elektrojupp/public_transport_map_berlin/hw/20xLED_001.kicad_sch

## KiCad design hw/20xLED_001.kicad_sch (2026-01-20)

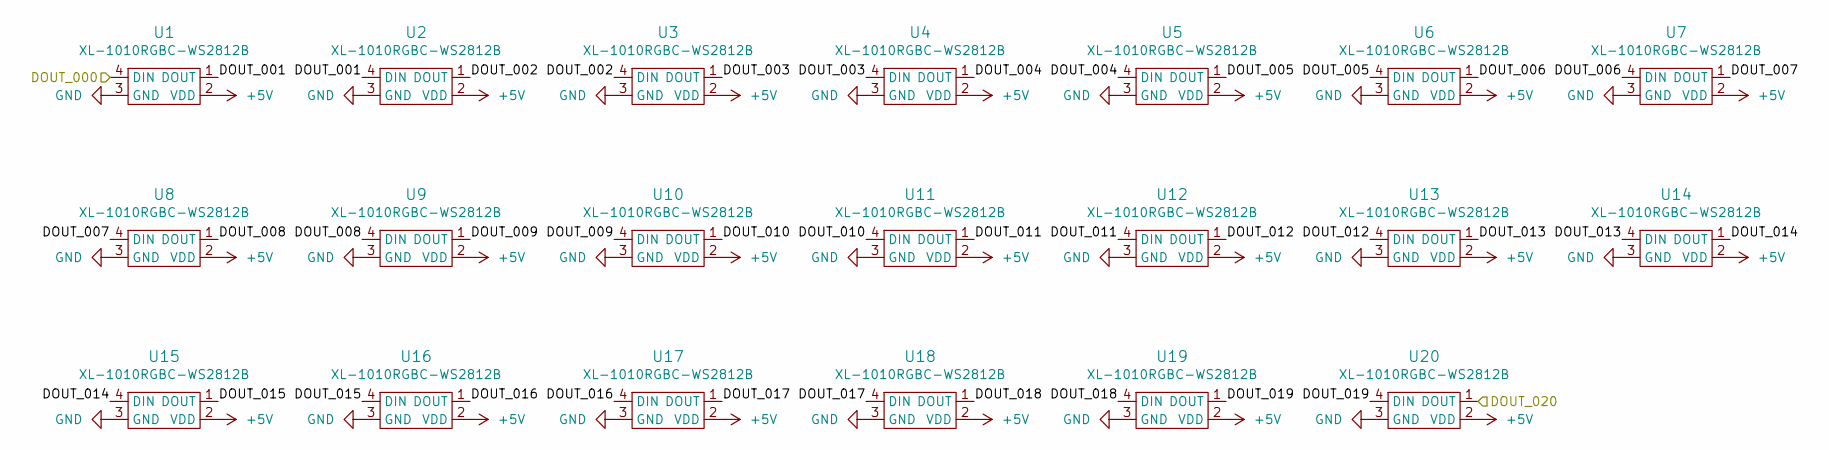
[picture p3: schematic 20xLED_001.kicad_sch]

Parts:
U1, U2, U3, U4, U5, U6, U7, U8, U9, U10, U11, U12, U13, U14, U15, U16, U17, U18, U19, U20: XL-1010RGBC-WS2812B; SMD-4P,1.1x1.1mm; LCSC C5349953

Connections:
+5V: U1.2 (VDD), U2.2 (VDD), U3.2 (VDD), U4.2 (VDD), U5.2 (VDD), U6.2 (VDD), U7.2 (VDD), U8.2 (VDD), U9.2 (VDD), U10.2 (VDD), U11.2 (VDD), U12.2 (VDD), U13.2 (VDD), U14.2 (VDD), U15.2 (VDD), U16.2 (VDD), U17.2 (VDD), U18.2 (VDD), U19.2 (VDD), U20.2 (VDD)
DOUT_000: U1.4 (DIN)
DOUT_001: U1.1 (DOUT), U2.4 (DIN)
DOUT_002: U2.1 (DOUT), U3.4 (DIN)
DOUT_003: U3.1 (DOUT), U4.4 (DIN)
DOUT_004: U4.1 (DOUT), U5.4 (DIN)
DOUT_005: U5.1 (DOUT), U6.4 (DIN)
DOUT_006: U6.1 (DOUT), U7.4 (DIN)
DOUT_007: U7.1 (DOUT), U8.4 (DIN)
DOUT_008: U8.1 (DOUT), U9.4 (DIN)
DOUT_009: U9.1 (DOUT), U10.4 (DIN)
DOUT_010: U10.1 (DOUT), U11.4 (DIN)
DOUT_011: U11.1 (DOUT), U12.4 (DIN)
DOUT_012: U12.1 (DOUT), U13.4 (DIN)
DOUT_013: U13.1 (DOUT), U14.4 (DIN)
DOUT_014: U14.1 (DOUT), U15.4 (DIN)
DOUT_015: U15.1 (DOUT), U16.4 (DIN)
DOUT_016: U16.1 (DOUT), U17.4 (DIN)
DOUT_017: U17.1 (DOUT), U18.4 (DIN)
DOUT_018: U18.1 (DOUT), U19.4 (DIN)
DOUT_019: U19.1 (DOUT), U20.4 (DIN)
DOUT_020: U20.1 (DOUT)
GND: U1.3 (GND), U2.3 (GND), U3.3 (GND), U4.3 (GND), U5.3 (GND), U6.3 (GND), U7.3 (GND), U8.3 (GND), U9.3 (GND), U10.3 (GND), U11.3 (GND), U12.3 (GND), U13.3 (GND), U14.3 (GND), U15.3 (GND), U16.3 (GND), U17.3 (GND), U18.3 (GND), U19.3 (GND), U20.3 (GND)
