elektrojupp/public_transport_map_berlin/hw/20xLED_002.kicad_sch

## KiCad design hw/20xLED_002.kicad_sch (2026-01-20)

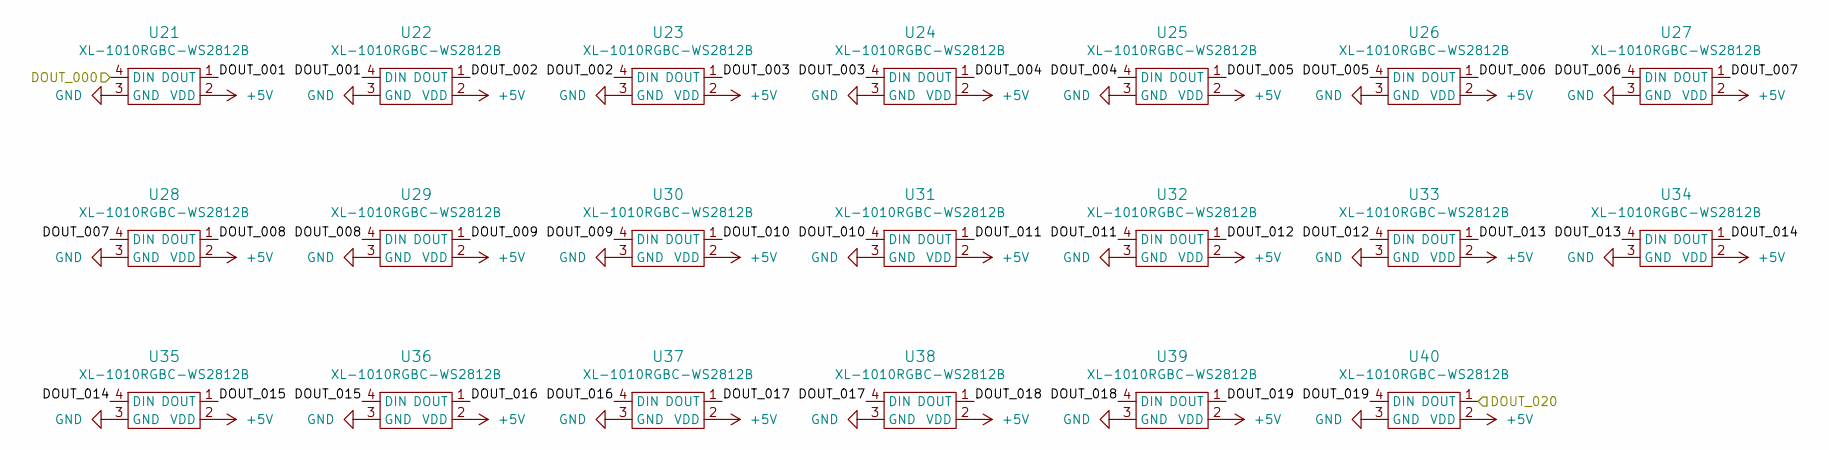
[picture p4: schematic 20xLED_002.kicad_sch]

Parts:
U21, U22, U23, U24, U25, U26, U27, U28, U29, U30, U31, U32, U33, U34, U35, U36, U37, U38, U39, U40: XL-1010RGBC-WS2812B; SMD-4P,1.1x1.1mm; LCSC C5349953

Connections:
+5V: U21.2 (VDD), U22.2 (VDD), U23.2 (VDD), U24.2 (VDD), U25.2 (VDD), U26.2 (VDD), U27.2 (VDD), U28.2 (VDD), U29.2 (VDD), U30.2 (VDD), U31.2 (VDD), U32.2 (VDD), U33.2 (VDD), U34.2 (VDD), U35.2 (VDD), U36.2 (VDD), U37.2 (VDD), U38.2 (VDD), U39.2 (VDD), U40.2 (VDD)
DOUT_000: U21.4 (DIN)
DOUT_001: U21.1 (DOUT), U22.4 (DIN)
DOUT_002: U22.1 (DOUT), U23.4 (DIN)
DOUT_003: U23.1 (DOUT), U24.4 (DIN)
DOUT_004: U24.1 (DOUT), U25.4 (DIN)
DOUT_005: U25.1 (DOUT), U26.4 (DIN)
DOUT_006: U26.1 (DOUT), U27.4 (DIN)
DOUT_007: U27.1 (DOUT), U28.4 (DIN)
DOUT_008: U28.1 (DOUT), U29.4 (DIN)
DOUT_009: U29.1 (DOUT), U30.4 (DIN)
DOUT_010: U30.1 (DOUT), U31.4 (DIN)
DOUT_011: U31.1 (DOUT), U32.4 (DIN)
DOUT_012: U32.1 (DOUT), U33.4 (DIN)
DOUT_013: U33.1 (DOUT), U34.4 (DIN)
DOUT_014: U34.1 (DOUT), U35.4 (DIN)
DOUT_015: U35.1 (DOUT), U36.4 (DIN)
DOUT_016: U36.1 (DOUT), U37.4 (DIN)
DOUT_017: U37.1 (DOUT), U38.4 (DIN)
DOUT_018: U38.1 (DOUT), U39.4 (DIN)
DOUT_019: U39.1 (DOUT), U40.4 (DIN)
DOUT_020: U40.1 (DOUT)
GND: U21.3 (GND), U22.3 (GND), U23.3 (GND), U24.3 (GND), U25.3 (GND), U26.3 (GND), U27.3 (GND), U28.3 (GND), U29.3 (GND), U30.3 (GND), U31.3 (GND), U32.3 (GND), U33.3 (GND), U34.3 (GND), U35.3 (GND), U36.3 (GND), U37.3 (GND), U38.3 (GND), U39.3 (GND), U40.3 (GND)
