elektrojupp/public_transport_map_berlin/hw/20xLED_003.kicad_sch

## KiCad design hw/20xLED_003.kicad_sch (2026-01-20)

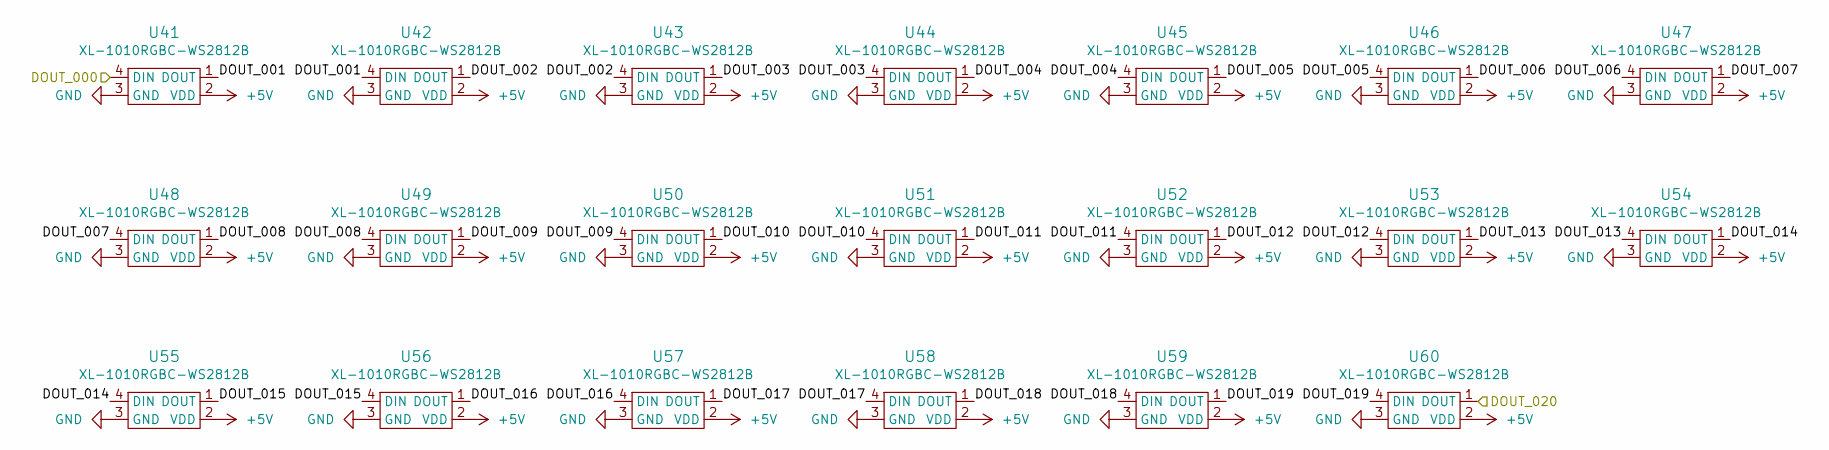
[picture p5: schematic 20xLED_003.kicad_sch]

Parts:
U41, U42, U43, U44, U45, U46, U47, U48, U49, U50, U51, U52, U53, U54, U55, U56, U57, U58, U59, U60: XL-1010RGBC-WS2812B; SMD-4P,1.1x1.1mm; LCSC C5349953

Connections:
+5V: U41.2 (VDD), U42.2 (VDD), U43.2 (VDD), U44.2 (VDD), U45.2 (VDD), U46.2 (VDD), U47.2 (VDD), U48.2 (VDD), U49.2 (VDD), U50.2 (VDD), U51.2 (VDD), U52.2 (VDD), U53.2 (VDD), U54.2 (VDD), U55.2 (VDD), U56.2 (VDD), U57.2 (VDD), U58.2 (VDD), U59.2 (VDD), U60.2 (VDD)
DOUT_000: U41.4 (DIN)
DOUT_001: U41.1 (DOUT), U42.4 (DIN)
DOUT_002: U42.1 (DOUT), U43.4 (DIN)
DOUT_003: U43.1 (DOUT), U44.4 (DIN)
DOUT_004: U44.1 (DOUT), U45.4 (DIN)
DOUT_005: U45.1 (DOUT), U46.4 (DIN)
DOUT_006: U46.1 (DOUT), U47.4 (DIN)
DOUT_007: U47.1 (DOUT), U48.4 (DIN)
DOUT_008: U48.1 (DOUT), U49.4 (DIN)
DOUT_009: U49.1 (DOUT), U50.4 (DIN)
DOUT_010: U50.1 (DOUT), U51.4 (DIN)
DOUT_011: U51.1 (DOUT), U52.4 (DIN)
DOUT_012: U52.1 (DOUT), U53.4 (DIN)
DOUT_013: U53.1 (DOUT), U54.4 (DIN)
DOUT_014: U54.1 (DOUT), U55.4 (DIN)
DOUT_015: U55.1 (DOUT), U56.4 (DIN)
DOUT_016: U56.1 (DOUT), U57.4 (DIN)
DOUT_017: U57.1 (DOUT), U58.4 (DIN)
DOUT_018: U58.1 (DOUT), U59.4 (DIN)
DOUT_019: U59.1 (DOUT), U60.4 (DIN)
DOUT_020: U60.1 (DOUT)
GND: U41.3 (GND), U42.3 (GND), U43.3 (GND), U44.3 (GND), U45.3 (GND), U46.3 (GND), U47.3 (GND), U48.3 (GND), U49.3 (GND), U50.3 (GND), U51.3 (GND), U52.3 (GND), U53.3 (GND), U54.3 (GND), U55.3 (GND), U56.3 (GND), U57.3 (GND), U58.3 (GND), U59.3 (GND), U60.3 (GND)
