elektrojupp/public_transport_map_berlin/hw/20xLED_004.kicad_sch

## KiCad design hw/20xLED_004.kicad_sch (2026-01-20)

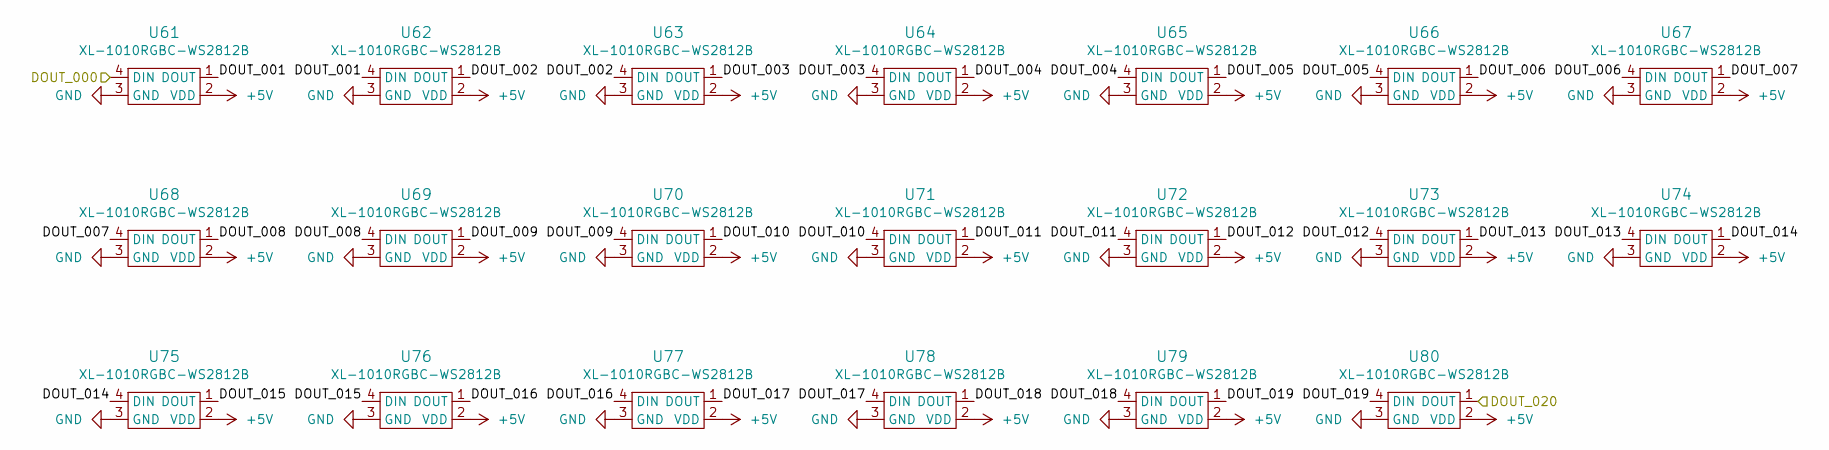
[picture p6: schematic 20xLED_004.kicad_sch]

Parts:
U61, U62, U63, U64, U65, U66, U67, U68, U69, U70, U71, U72, U73, U74, U75, U76, U77, U78, U79, U80: XL-1010RGBC-WS2812B; SMD-4P,1.1x1.1mm; LCSC C5349953

Connections:
+5V: U61.2 (VDD), U62.2 (VDD), U63.2 (VDD), U64.2 (VDD), U65.2 (VDD), U66.2 (VDD), U67.2 (VDD), U68.2 (VDD), U69.2 (VDD), U70.2 (VDD), U71.2 (VDD), U72.2 (VDD), U73.2 (VDD), U74.2 (VDD), U75.2 (VDD), U76.2 (VDD), U77.2 (VDD), U78.2 (VDD), U79.2 (VDD), U80.2 (VDD)
DOUT_000: U61.4 (DIN)
DOUT_001: U61.1 (DOUT), U62.4 (DIN)
DOUT_002: U62.1 (DOUT), U63.4 (DIN)
DOUT_003: U63.1 (DOUT), U64.4 (DIN)
DOUT_004: U64.1 (DOUT), U65.4 (DIN)
DOUT_005: U65.1 (DOUT), U66.4 (DIN)
DOUT_006: U66.1 (DOUT), U67.4 (DIN)
DOUT_007: U67.1 (DOUT), U68.4 (DIN)
DOUT_008: U68.1 (DOUT), U69.4 (DIN)
DOUT_009: U69.1 (DOUT), U70.4 (DIN)
DOUT_010: U70.1 (DOUT), U71.4 (DIN)
DOUT_011: U71.1 (DOUT), U72.4 (DIN)
DOUT_012: U72.1 (DOUT), U73.4 (DIN)
DOUT_013: U73.1 (DOUT), U74.4 (DIN)
DOUT_014: U74.1 (DOUT), U75.4 (DIN)
DOUT_015: U75.1 (DOUT), U76.4 (DIN)
DOUT_016: U76.1 (DOUT), U77.4 (DIN)
DOUT_017: U77.1 (DOUT), U78.4 (DIN)
DOUT_018: U78.1 (DOUT), U79.4 (DIN)
DOUT_019: U79.1 (DOUT), U80.4 (DIN)
DOUT_020: U80.1 (DOUT)
GND: U61.3 (GND), U62.3 (GND), U63.3 (GND), U64.3 (GND), U65.3 (GND), U66.3 (GND), U67.3 (GND), U68.3 (GND), U69.3 (GND), U70.3 (GND), U71.3 (GND), U72.3 (GND), U73.3 (GND), U74.3 (GND), U75.3 (GND), U76.3 (GND), U77.3 (GND), U78.3 (GND), U79.3 (GND), U80.3 (GND)
