elektrojupp/public_transport_map_berlin/hw/20xLED_005.kicad_sch

## KiCad design hw/20xLED_005.kicad_sch (2026-01-20)

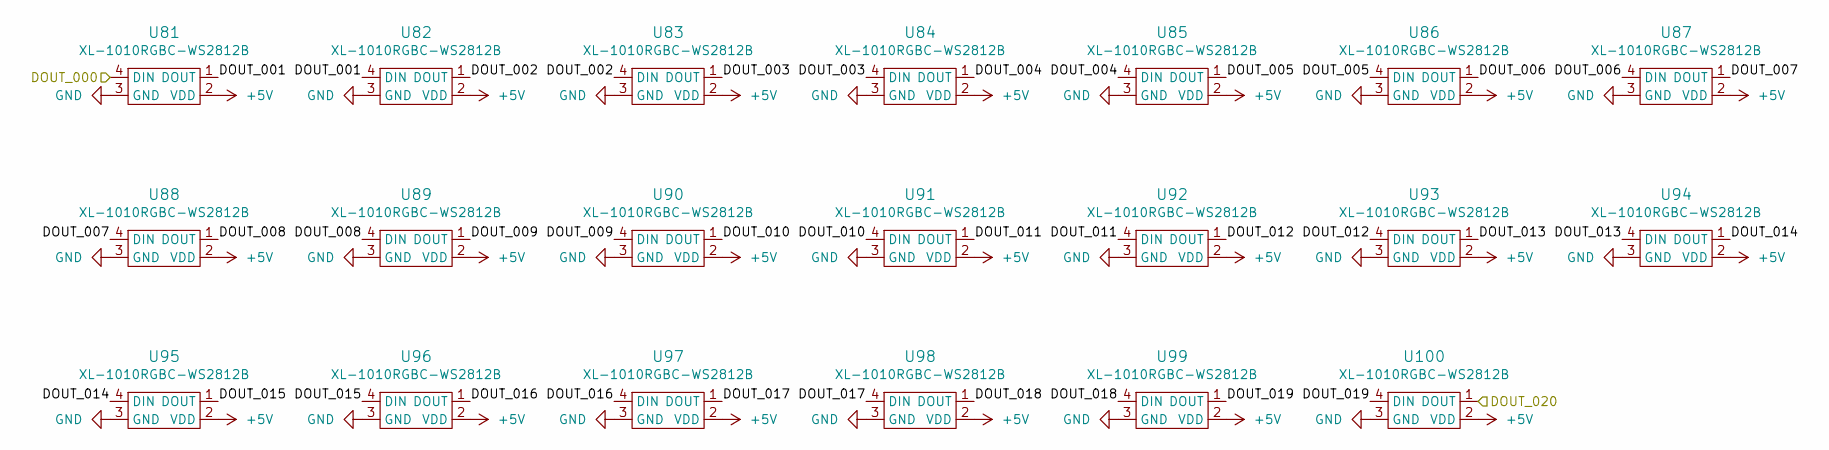
[picture p7: schematic 20xLED_005.kicad_sch]

Parts:
U81, U82, U83, U84, U85, U86, U87, U88, U89, U90, U91, U92, U93, U94, U95, U96, U97, U98, U99, U100: XL-1010RGBC-WS2812B; SMD-4P,1.1x1.1mm; LCSC C5349953

Connections:
+5V: U81.2 (VDD), U82.2 (VDD), U83.2 (VDD), U84.2 (VDD), U85.2 (VDD), U86.2 (VDD), U87.2 (VDD), U88.2 (VDD), U89.2 (VDD), U90.2 (VDD), U91.2 (VDD), U92.2 (VDD), U93.2 (VDD), U94.2 (VDD), U95.2 (VDD), U96.2 (VDD), U97.2 (VDD), U98.2 (VDD), U99.2 (VDD), U100.2 (VDD)
DOUT_000: U81.4 (DIN)
DOUT_001: U81.1 (DOUT), U82.4 (DIN)
DOUT_002: U82.1 (DOUT), U83.4 (DIN)
DOUT_003: U83.1 (DOUT), U84.4 (DIN)
DOUT_004: U84.1 (DOUT), U85.4 (DIN)
DOUT_005: U85.1 (DOUT), U86.4 (DIN)
DOUT_006: U86.1 (DOUT), U87.4 (DIN)
DOUT_007: U87.1 (DOUT), U88.4 (DIN)
DOUT_008: U88.1 (DOUT), U89.4 (DIN)
DOUT_009: U89.1 (DOUT), U90.4 (DIN)
DOUT_010: U90.1 (DOUT), U91.4 (DIN)
DOUT_011: U91.1 (DOUT), U92.4 (DIN)
DOUT_012: U92.1 (DOUT), U93.4 (DIN)
DOUT_013: U93.1 (DOUT), U94.4 (DIN)
DOUT_014: U94.1 (DOUT), U95.4 (DIN)
DOUT_015: U95.1 (DOUT), U96.4 (DIN)
DOUT_016: U96.1 (DOUT), U97.4 (DIN)
DOUT_017: U97.1 (DOUT), U98.4 (DIN)
DOUT_018: U98.1 (DOUT), U99.4 (DIN)
DOUT_019: U99.1 (DOUT), U100.4 (DIN)
DOUT_020: U100.1 (DOUT)
GND: U81.3 (GND), U82.3 (GND), U83.3 (GND), U84.3 (GND), U85.3 (GND), U86.3 (GND), U87.3 (GND), U88.3 (GND), U89.3 (GND), U90.3 (GND), U91.3 (GND), U92.3 (GND), U93.3 (GND), U94.3 (GND), U95.3 (GND), U96.3 (GND), U97.3 (GND), U98.3 (GND), U99.3 (GND), U100.3 (GND)
