elektrojupp/public_transport_map_berlin/hw/20xLED_006.kicad_sch

## KiCad design hw/20xLED_006.kicad_sch (2026-01-20)

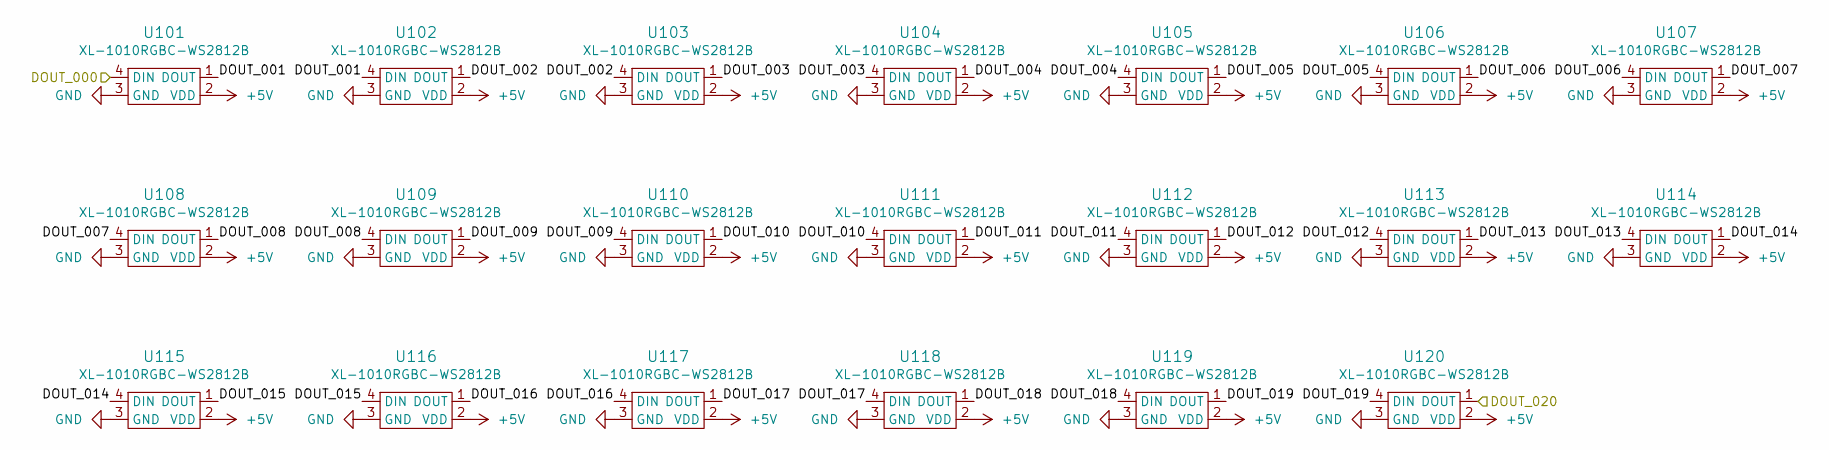
[picture p8: schematic 20xLED_006.kicad_sch]

Parts:
U101, U102, U103, U104, U105, U106, U107, U108, U109, U110, U111, U112, U113, U114, U115, U116, U117, U118, U119, U120: XL-1010RGBC-WS2812B; SMD-4P,1.1x1.1mm; LCSC C5349953

Connections:
+5V: U101.2 (VDD), U102.2 (VDD), U103.2 (VDD), U104.2 (VDD), U105.2 (VDD), U106.2 (VDD), U107.2 (VDD), U108.2 (VDD), U109.2 (VDD), U110.2 (VDD), U111.2 (VDD), U112.2 (VDD), U113.2 (VDD), U114.2 (VDD), U115.2 (VDD), U116.2 (VDD), U117.2 (VDD), U118.2 (VDD), U119.2 (VDD), U120.2 (VDD)
DOUT_000: U101.4 (DIN)
DOUT_001: U101.1 (DOUT), U102.4 (DIN)
DOUT_002: U102.1 (DOUT), U103.4 (DIN)
DOUT_003: U103.1 (DOUT), U104.4 (DIN)
DOUT_004: U104.1 (DOUT), U105.4 (DIN)
DOUT_005: U105.1 (DOUT), U106.4 (DIN)
DOUT_006: U106.1 (DOUT), U107.4 (DIN)
DOUT_007: U107.1 (DOUT), U108.4 (DIN)
DOUT_008: U108.1 (DOUT), U109.4 (DIN)
DOUT_009: U109.1 (DOUT), U110.4 (DIN)
DOUT_010: U110.1 (DOUT), U111.4 (DIN)
DOUT_011: U111.1 (DOUT), U112.4 (DIN)
DOUT_012: U112.1 (DOUT), U113.4 (DIN)
DOUT_013: U113.1 (DOUT), U114.4 (DIN)
DOUT_014: U114.1 (DOUT), U115.4 (DIN)
DOUT_015: U115.1 (DOUT), U116.4 (DIN)
DOUT_016: U116.1 (DOUT), U117.4 (DIN)
DOUT_017: U117.1 (DOUT), U118.4 (DIN)
DOUT_018: U118.1 (DOUT), U119.4 (DIN)
DOUT_019: U119.1 (DOUT), U120.4 (DIN)
DOUT_020: U120.1 (DOUT)
GND: U101.3 (GND), U102.3 (GND), U103.3 (GND), U104.3 (GND), U105.3 (GND), U106.3 (GND), U107.3 (GND), U108.3 (GND), U109.3 (GND), U110.3 (GND), U111.3 (GND), U112.3 (GND), U113.3 (GND), U114.3 (GND), U115.3 (GND), U116.3 (GND), U117.3 (GND), U118.3 (GND), U119.3 (GND), U120.3 (GND)
