elektrojupp/public_transport_map_berlin/hw/20xLED_007.kicad_sch

## KiCad design hw/20xLED_007.kicad_sch (2026-01-20)

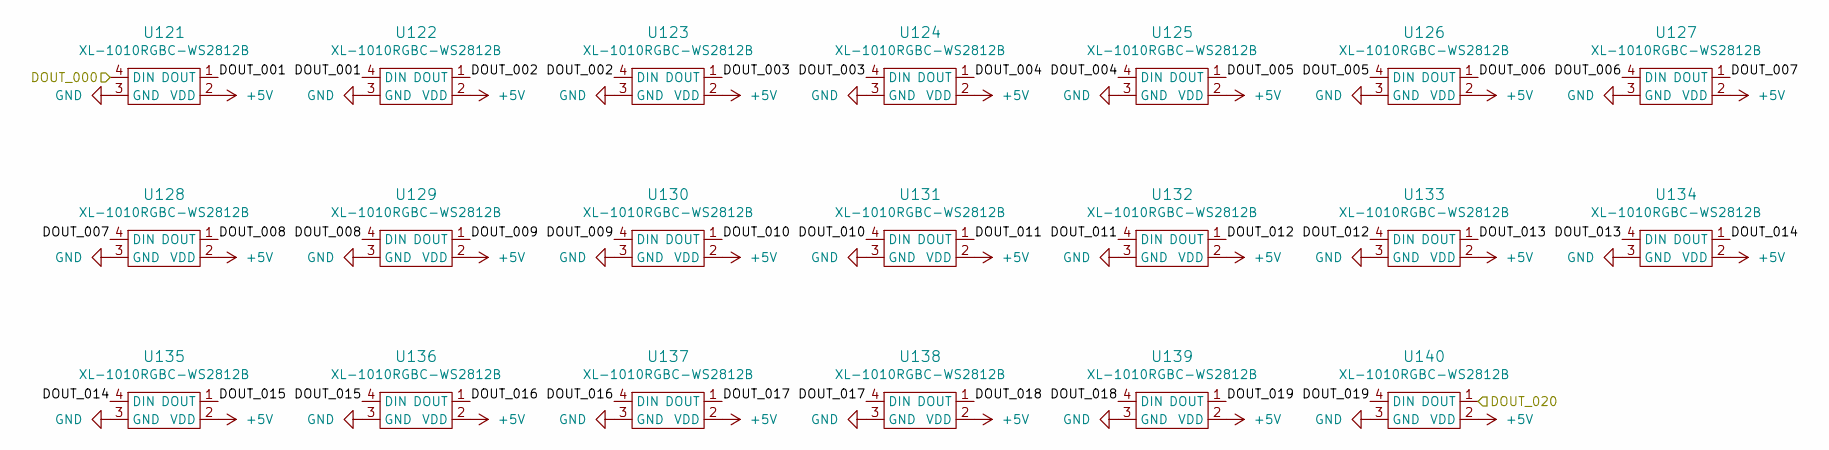
[picture p9: schematic 20xLED_007.kicad_sch]

Parts:
U121, U122, U123, U124, U125, U126, U127, U128, U129, U130, U131, U132, U133, U134, U135, U136, U137, U138, U139, U140: XL-1010RGBC-WS2812B; SMD-4P,1.1x1.1mm; LCSC C5349953

Connections:
+5V: U121.2 (VDD), U122.2 (VDD), U123.2 (VDD), U124.2 (VDD), U125.2 (VDD), U126.2 (VDD), U127.2 (VDD), U128.2 (VDD), U129.2 (VDD), U130.2 (VDD), U131.2 (VDD), U132.2 (VDD), U133.2 (VDD), U134.2 (VDD), U135.2 (VDD), U136.2 (VDD), U137.2 (VDD), U138.2 (VDD), U139.2 (VDD), U140.2 (VDD)
DOUT_000: U121.4 (DIN)
DOUT_001: U121.1 (DOUT), U122.4 (DIN)
DOUT_002: U122.1 (DOUT), U123.4 (DIN)
DOUT_003: U123.1 (DOUT), U124.4 (DIN)
DOUT_004: U124.1 (DOUT), U125.4 (DIN)
DOUT_005: U125.1 (DOUT), U126.4 (DIN)
DOUT_006: U126.1 (DOUT), U127.4 (DIN)
DOUT_007: U127.1 (DOUT), U128.4 (DIN)
DOUT_008: U128.1 (DOUT), U129.4 (DIN)
DOUT_009: U129.1 (DOUT), U130.4 (DIN)
DOUT_010: U130.1 (DOUT), U131.4 (DIN)
DOUT_011: U131.1 (DOUT), U132.4 (DIN)
DOUT_012: U132.1 (DOUT), U133.4 (DIN)
DOUT_013: U133.1 (DOUT), U134.4 (DIN)
DOUT_014: U134.1 (DOUT), U135.4 (DIN)
DOUT_015: U135.1 (DOUT), U136.4 (DIN)
DOUT_016: U136.1 (DOUT), U137.4 (DIN)
DOUT_017: U137.1 (DOUT), U138.4 (DIN)
DOUT_018: U138.1 (DOUT), U139.4 (DIN)
DOUT_019: U139.1 (DOUT), U140.4 (DIN)
DOUT_020: U140.1 (DOUT)
GND: U121.3 (GND), U122.3 (GND), U123.3 (GND), U124.3 (GND), U125.3 (GND), U126.3 (GND), U127.3 (GND), U128.3 (GND), U129.3 (GND), U130.3 (GND), U131.3 (GND), U132.3 (GND), U133.3 (GND), U134.3 (GND), U135.3 (GND), U136.3 (GND), U137.3 (GND), U138.3 (GND), U139.3 (GND), U140.3 (GND)
