elektrojupp/public_transport_map_berlin/hw/20xLED_008.kicad_sch

## KiCad design hw/20xLED_008.kicad_sch (2026-01-20)

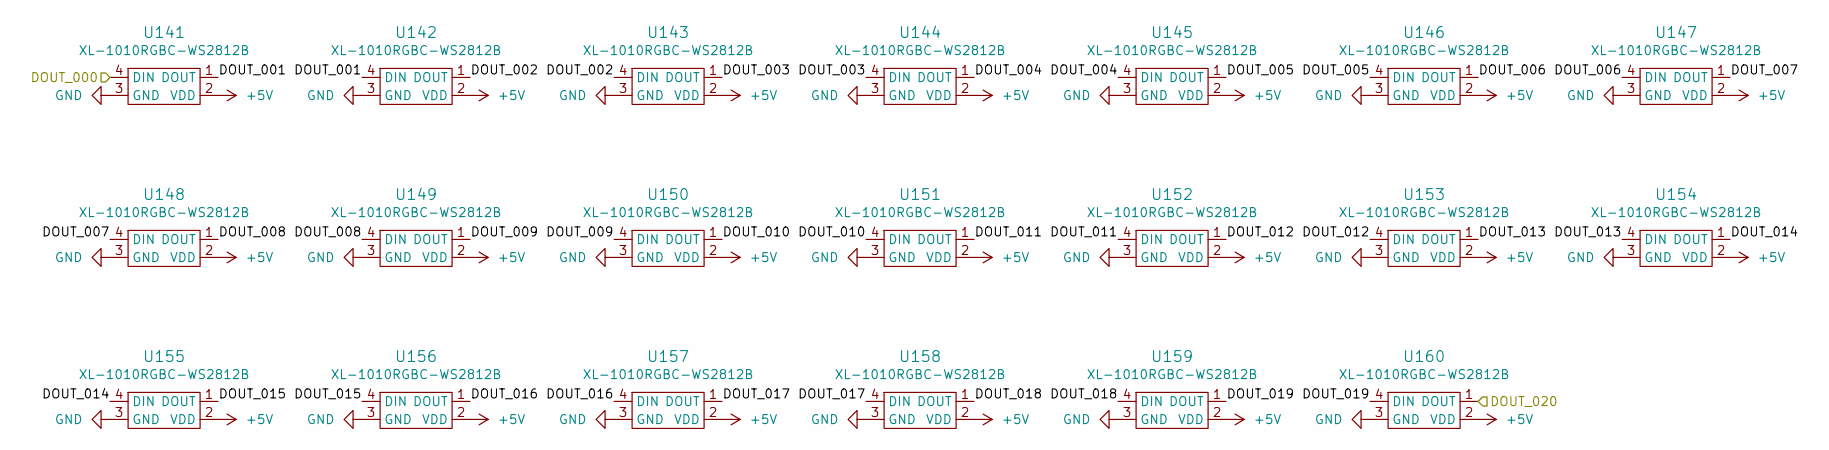
[picture p10: schematic 20xLED_008.kicad_sch]

Parts:
U141, U142, U143, U144, U145, U146, U147, U148, U149, U150, U151, U152, U153, U154, U155, U156, U157, U158, U159, U160: XL-1010RGBC-WS2812B; SMD-4P,1.1x1.1mm; LCSC C5349953

Connections:
+5V: U141.2 (VDD), U142.2 (VDD), U143.2 (VDD), U144.2 (VDD), U145.2 (VDD), U146.2 (VDD), U147.2 (VDD), U148.2 (VDD), U149.2 (VDD), U150.2 (VDD), U151.2 (VDD), U152.2 (VDD), U153.2 (VDD), U154.2 (VDD), U155.2 (VDD), U156.2 (VDD), U157.2 (VDD), U158.2 (VDD), U159.2 (VDD), U160.2 (VDD)
DOUT_000: U141.4 (DIN)
DOUT_001: U141.1 (DOUT), U142.4 (DIN)
DOUT_002: U142.1 (DOUT), U143.4 (DIN)
DOUT_003: U143.1 (DOUT), U144.4 (DIN)
DOUT_004: U144.1 (DOUT), U145.4 (DIN)
DOUT_005: U145.1 (DOUT), U146.4 (DIN)
DOUT_006: U146.1 (DOUT), U147.4 (DIN)
DOUT_007: U147.1 (DOUT), U148.4 (DIN)
DOUT_008: U148.1 (DOUT), U149.4 (DIN)
DOUT_009: U149.1 (DOUT), U150.4 (DIN)
DOUT_010: U150.1 (DOUT), U151.4 (DIN)
DOUT_011: U151.1 (DOUT), U152.4 (DIN)
DOUT_012: U152.1 (DOUT), U153.4 (DIN)
DOUT_013: U153.1 (DOUT), U154.4 (DIN)
DOUT_014: U154.1 (DOUT), U155.4 (DIN)
DOUT_015: U155.1 (DOUT), U156.4 (DIN)
DOUT_016: U156.1 (DOUT), U157.4 (DIN)
DOUT_017: U157.1 (DOUT), U158.4 (DIN)
DOUT_018: U158.1 (DOUT), U159.4 (DIN)
DOUT_019: U159.1 (DOUT), U160.4 (DIN)
DOUT_020: U160.1 (DOUT)
GND: U141.3 (GND), U142.3 (GND), U143.3 (GND), U144.3 (GND), U145.3 (GND), U146.3 (GND), U147.3 (GND), U148.3 (GND), U149.3 (GND), U150.3 (GND), U151.3 (GND), U152.3 (GND), U153.3 (GND), U154.3 (GND), U155.3 (GND), U156.3 (GND), U157.3 (GND), U158.3 (GND), U159.3 (GND), U160.3 (GND)
