elektrojupp/public_transport_map_berlin/hw/20xLED_009.kicad_sch

## KiCad design hw/20xLED_009.kicad_sch (2026-01-20)

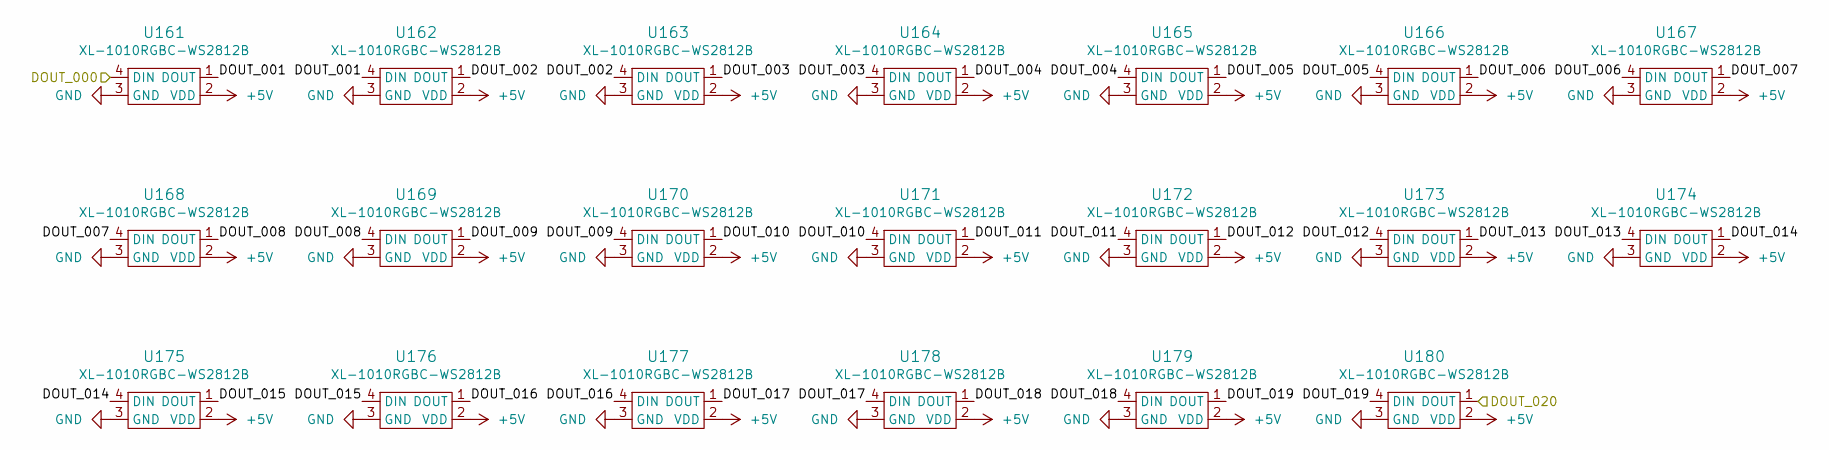
[picture p11: schematic 20xLED_009.kicad_sch]

Parts:
U161, U162, U163, U164, U165, U166, U167, U168, U169, U170, U171, U172, U173, U174, U175, U176, U177, U178, U179, U180: XL-1010RGBC-WS2812B; SMD-4P,1.1x1.1mm; LCSC C5349953

Connections:
+5V: U161.2 (VDD), U162.2 (VDD), U163.2 (VDD), U164.2 (VDD), U165.2 (VDD), U166.2 (VDD), U167.2 (VDD), U168.2 (VDD), U169.2 (VDD), U170.2 (VDD), U171.2 (VDD), U172.2 (VDD), U173.2 (VDD), U174.2 (VDD), U175.2 (VDD), U176.2 (VDD), U177.2 (VDD), U178.2 (VDD), U179.2 (VDD), U180.2 (VDD)
DOUT_000: U161.4 (DIN)
DOUT_001: U161.1 (DOUT), U162.4 (DIN)
DOUT_002: U162.1 (DOUT), U163.4 (DIN)
DOUT_003: U163.1 (DOUT), U164.4 (DIN)
DOUT_004: U164.1 (DOUT), U165.4 (DIN)
DOUT_005: U165.1 (DOUT), U166.4 (DIN)
DOUT_006: U166.1 (DOUT), U167.4 (DIN)
DOUT_007: U167.1 (DOUT), U168.4 (DIN)
DOUT_008: U168.1 (DOUT), U169.4 (DIN)
DOUT_009: U169.1 (DOUT), U170.4 (DIN)
DOUT_010: U170.1 (DOUT), U171.4 (DIN)
DOUT_011: U171.1 (DOUT), U172.4 (DIN)
DOUT_012: U172.1 (DOUT), U173.4 (DIN)
DOUT_013: U173.1 (DOUT), U174.4 (DIN)
DOUT_014: U174.1 (DOUT), U175.4 (DIN)
DOUT_015: U175.1 (DOUT), U176.4 (DIN)
DOUT_016: U176.1 (DOUT), U177.4 (DIN)
DOUT_017: U177.1 (DOUT), U178.4 (DIN)
DOUT_018: U178.1 (DOUT), U179.4 (DIN)
DOUT_019: U179.1 (DOUT), U180.4 (DIN)
DOUT_020: U180.1 (DOUT)
GND: U161.3 (GND), U162.3 (GND), U163.3 (GND), U164.3 (GND), U165.3 (GND), U166.3 (GND), U167.3 (GND), U168.3 (GND), U169.3 (GND), U170.3 (GND), U171.3 (GND), U172.3 (GND), U173.3 (GND), U174.3 (GND), U175.3 (GND), U176.3 (GND), U177.3 (GND), U178.3 (GND), U179.3 (GND), U180.3 (GND)
