elektrojupp/public_transport_map_berlin/hw/20xLED_010.kicad_sch

## KiCad design hw/20xLED_010.kicad_sch (2026-01-20)

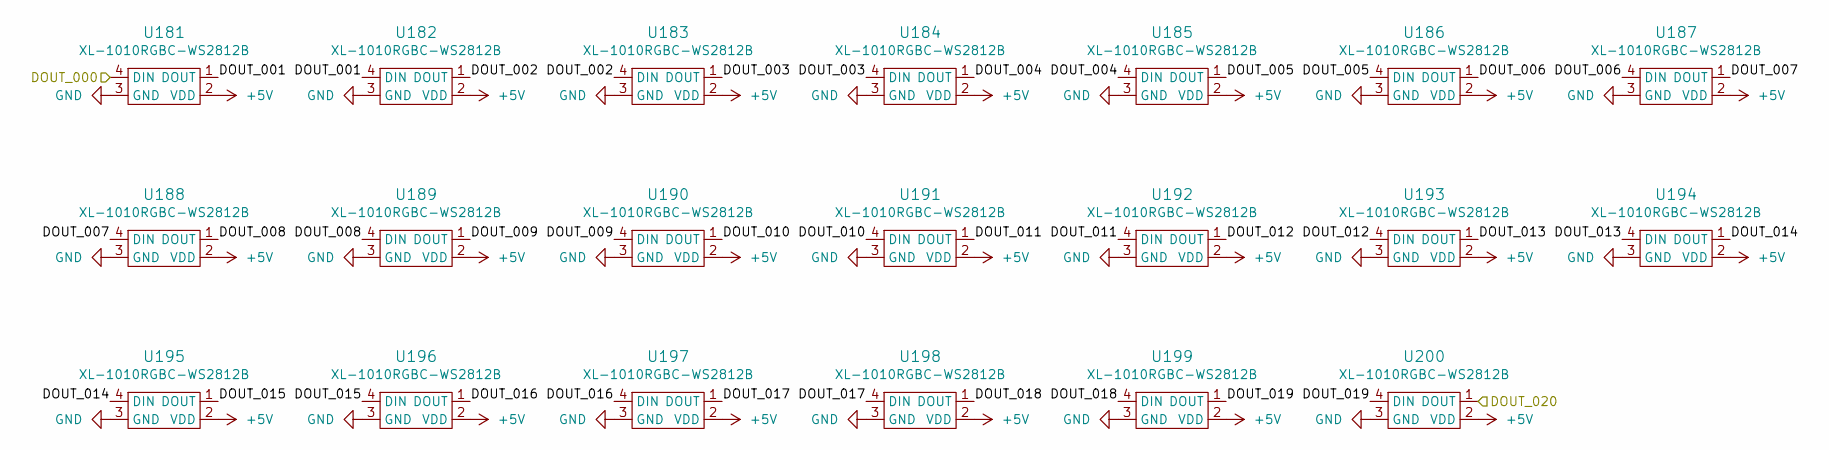
[picture p12: schematic 20xLED_010.kicad_sch]

Parts:
U181, U182, U183, U184, U185, U186, U187, U188, U189, U190, U191, U192, U193, U194, U195, U196, U197, U198, U199, U200: XL-1010RGBC-WS2812B; SMD-4P,1.1x1.1mm; LCSC C5349953

Connections:
+5V: U181.2 (VDD), U182.2 (VDD), U183.2 (VDD), U184.2 (VDD), U185.2 (VDD), U186.2 (VDD), U187.2 (VDD), U188.2 (VDD), U189.2 (VDD), U190.2 (VDD), U191.2 (VDD), U192.2 (VDD), U193.2 (VDD), U194.2 (VDD), U195.2 (VDD), U196.2 (VDD), U197.2 (VDD), U198.2 (VDD), U199.2 (VDD), U200.2 (VDD)
DOUT_000: U181.4 (DIN)
DOUT_001: U181.1 (DOUT), U182.4 (DIN)
DOUT_002: U182.1 (DOUT), U183.4 (DIN)
DOUT_003: U183.1 (DOUT), U184.4 (DIN)
DOUT_004: U184.1 (DOUT), U185.4 (DIN)
DOUT_005: U185.1 (DOUT), U186.4 (DIN)
DOUT_006: U186.1 (DOUT), U187.4 (DIN)
DOUT_007: U187.1 (DOUT), U188.4 (DIN)
DOUT_008: U188.1 (DOUT), U189.4 (DIN)
DOUT_009: U189.1 (DOUT), U190.4 (DIN)
DOUT_010: U190.1 (DOUT), U191.4 (DIN)
DOUT_011: U191.1 (DOUT), U192.4 (DIN)
DOUT_012: U192.1 (DOUT), U193.4 (DIN)
DOUT_013: U193.1 (DOUT), U194.4 (DIN)
DOUT_014: U194.1 (DOUT), U195.4 (DIN)
DOUT_015: U195.1 (DOUT), U196.4 (DIN)
DOUT_016: U196.1 (DOUT), U197.4 (DIN)
DOUT_017: U197.1 (DOUT), U198.4 (DIN)
DOUT_018: U198.1 (DOUT), U199.4 (DIN)
DOUT_019: U199.1 (DOUT), U200.4 (DIN)
DOUT_020: U200.1 (DOUT)
GND: U181.3 (GND), U182.3 (GND), U183.3 (GND), U184.3 (GND), U185.3 (GND), U186.3 (GND), U187.3 (GND), U188.3 (GND), U189.3 (GND), U190.3 (GND), U191.3 (GND), U192.3 (GND), U193.3 (GND), U194.3 (GND), U195.3 (GND), U196.3 (GND), U197.3 (GND), U198.3 (GND), U199.3 (GND), U200.3 (GND)
