elektrojupp/public_transport_map_berlin/hw/20xLED_011.kicad_sch

## KiCad design hw/20xLED_011.kicad_sch (2026-01-20)

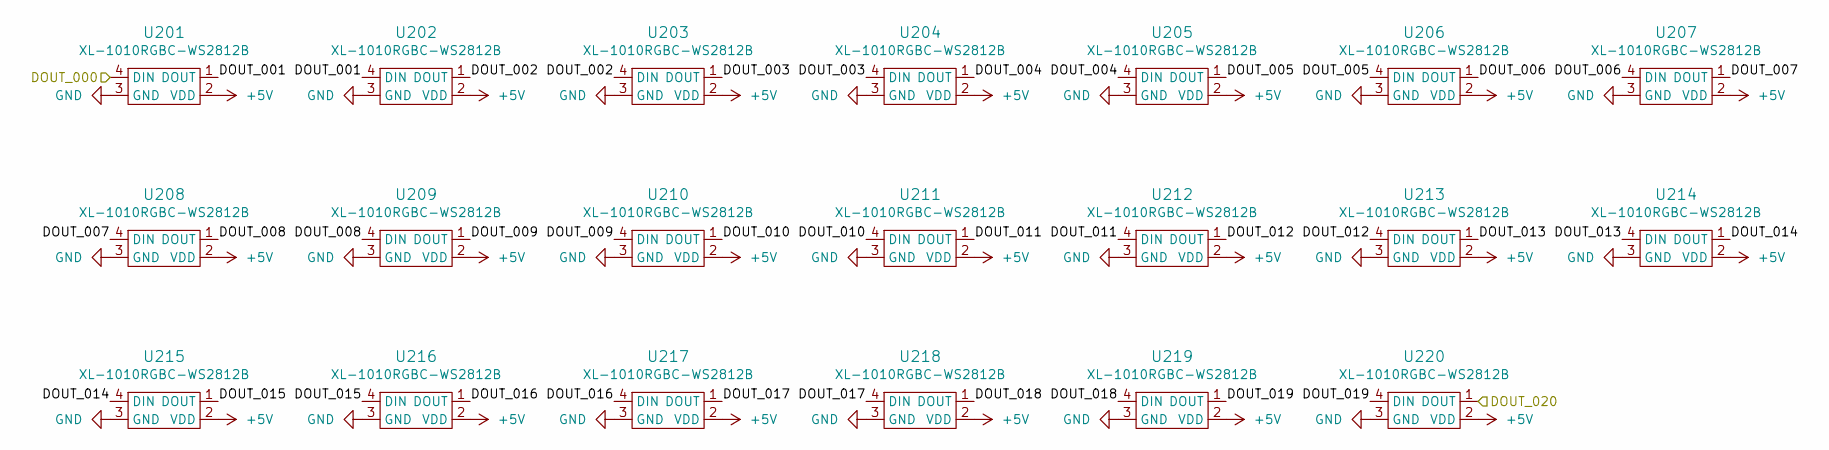
[picture p13: schematic 20xLED_011.kicad_sch]

Parts:
U201, U202, U203, U204, U205, U206, U207, U208, U209, U210, U211, U212, U213, U214, U215, U216, U217, U218, U219, U220: XL-1010RGBC-WS2812B; SMD-4P,1.1x1.1mm; LCSC C5349953

Connections:
+5V: U201.2 (VDD), U202.2 (VDD), U203.2 (VDD), U204.2 (VDD), U205.2 (VDD), U206.2 (VDD), U207.2 (VDD), U208.2 (VDD), U209.2 (VDD), U210.2 (VDD), U211.2 (VDD), U212.2 (VDD), U213.2 (VDD), U214.2 (VDD), U215.2 (VDD), U216.2 (VDD), U217.2 (VDD), U218.2 (VDD), U219.2 (VDD), U220.2 (VDD)
DOUT_000: U201.4 (DIN)
DOUT_001: U201.1 (DOUT), U202.4 (DIN)
DOUT_002: U202.1 (DOUT), U203.4 (DIN)
DOUT_003: U203.1 (DOUT), U204.4 (DIN)
DOUT_004: U204.1 (DOUT), U205.4 (DIN)
DOUT_005: U205.1 (DOUT), U206.4 (DIN)
DOUT_006: U206.1 (DOUT), U207.4 (DIN)
DOUT_007: U207.1 (DOUT), U208.4 (DIN)
DOUT_008: U208.1 (DOUT), U209.4 (DIN)
DOUT_009: U209.1 (DOUT), U210.4 (DIN)
DOUT_010: U210.1 (DOUT), U211.4 (DIN)
DOUT_011: U211.1 (DOUT), U212.4 (DIN)
DOUT_012: U212.1 (DOUT), U213.4 (DIN)
DOUT_013: U213.1 (DOUT), U214.4 (DIN)
DOUT_014: U214.1 (DOUT), U215.4 (DIN)
DOUT_015: U215.1 (DOUT), U216.4 (DIN)
DOUT_016: U216.1 (DOUT), U217.4 (DIN)
DOUT_017: U217.1 (DOUT), U218.4 (DIN)
DOUT_018: U218.1 (DOUT), U219.4 (DIN)
DOUT_019: U219.1 (DOUT), U220.4 (DIN)
DOUT_020: U220.1 (DOUT)
GND: U201.3 (GND), U202.3 (GND), U203.3 (GND), U204.3 (GND), U205.3 (GND), U206.3 (GND), U207.3 (GND), U208.3 (GND), U209.3 (GND), U210.3 (GND), U211.3 (GND), U212.3 (GND), U213.3 (GND), U214.3 (GND), U215.3 (GND), U216.3 (GND), U217.3 (GND), U218.3 (GND), U219.3 (GND), U220.3 (GND)
