elektrojupp/public_transport_map_berlin/hw/20xLED_012.kicad_sch

## KiCad design hw/20xLED_012.kicad_sch (2026-01-20)

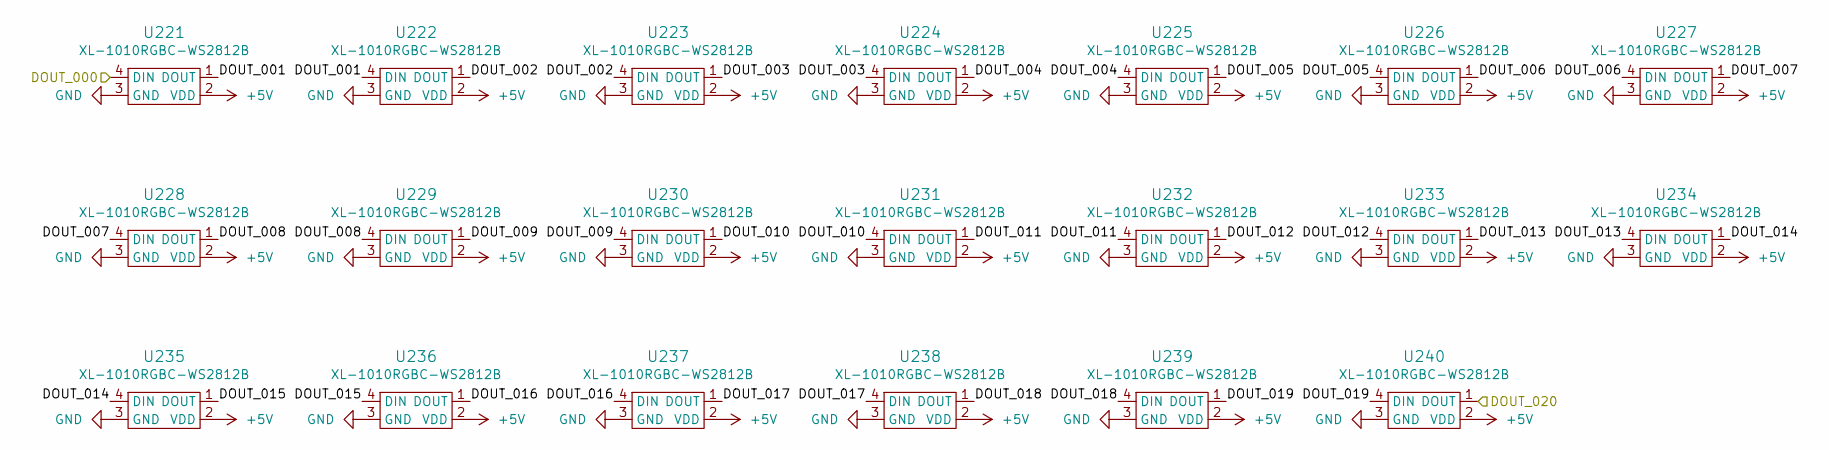
[picture p14: schematic 20xLED_012.kicad_sch]

Parts:
U221, U222, U223, U224, U225, U226, U227, U228, U229, U230, U231, U232, U233, U234, U235, U236, U237, U238, U239, U240: XL-1010RGBC-WS2812B; SMD-4P,1.1x1.1mm; LCSC C5349953

Connections:
+5V: U221.2 (VDD), U222.2 (VDD), U223.2 (VDD), U224.2 (VDD), U225.2 (VDD), U226.2 (VDD), U227.2 (VDD), U228.2 (VDD), U229.2 (VDD), U230.2 (VDD), U231.2 (VDD), U232.2 (VDD), U233.2 (VDD), U234.2 (VDD), U235.2 (VDD), U236.2 (VDD), U237.2 (VDD), U238.2 (VDD), U239.2 (VDD), U240.2 (VDD)
DOUT_000: U221.4 (DIN)
DOUT_001: U221.1 (DOUT), U222.4 (DIN)
DOUT_002: U222.1 (DOUT), U223.4 (DIN)
DOUT_003: U223.1 (DOUT), U224.4 (DIN)
DOUT_004: U224.1 (DOUT), U225.4 (DIN)
DOUT_005: U225.1 (DOUT), U226.4 (DIN)
DOUT_006: U226.1 (DOUT), U227.4 (DIN)
DOUT_007: U227.1 (DOUT), U228.4 (DIN)
DOUT_008: U228.1 (DOUT), U229.4 (DIN)
DOUT_009: U229.1 (DOUT), U230.4 (DIN)
DOUT_010: U230.1 (DOUT), U231.4 (DIN)
DOUT_011: U231.1 (DOUT), U232.4 (DIN)
DOUT_012: U232.1 (DOUT), U233.4 (DIN)
DOUT_013: U233.1 (DOUT), U234.4 (DIN)
DOUT_014: U234.1 (DOUT), U235.4 (DIN)
DOUT_015: U235.1 (DOUT), U236.4 (DIN)
DOUT_016: U236.1 (DOUT), U237.4 (DIN)
DOUT_017: U237.1 (DOUT), U238.4 (DIN)
DOUT_018: U238.1 (DOUT), U239.4 (DIN)
DOUT_019: U239.1 (DOUT), U240.4 (DIN)
DOUT_020: U240.1 (DOUT)
GND: U221.3 (GND), U222.3 (GND), U223.3 (GND), U224.3 (GND), U225.3 (GND), U226.3 (GND), U227.3 (GND), U228.3 (GND), U229.3 (GND), U230.3 (GND), U231.3 (GND), U232.3 (GND), U233.3 (GND), U234.3 (GND), U235.3 (GND), U236.3 (GND), U237.3 (GND), U238.3 (GND), U239.3 (GND), U240.3 (GND)
