elektrojupp/public_transport_map_berlin/hw/20xLED_013.kicad_sch

## KiCad design hw/20xLED_013.kicad_sch (2026-01-20)

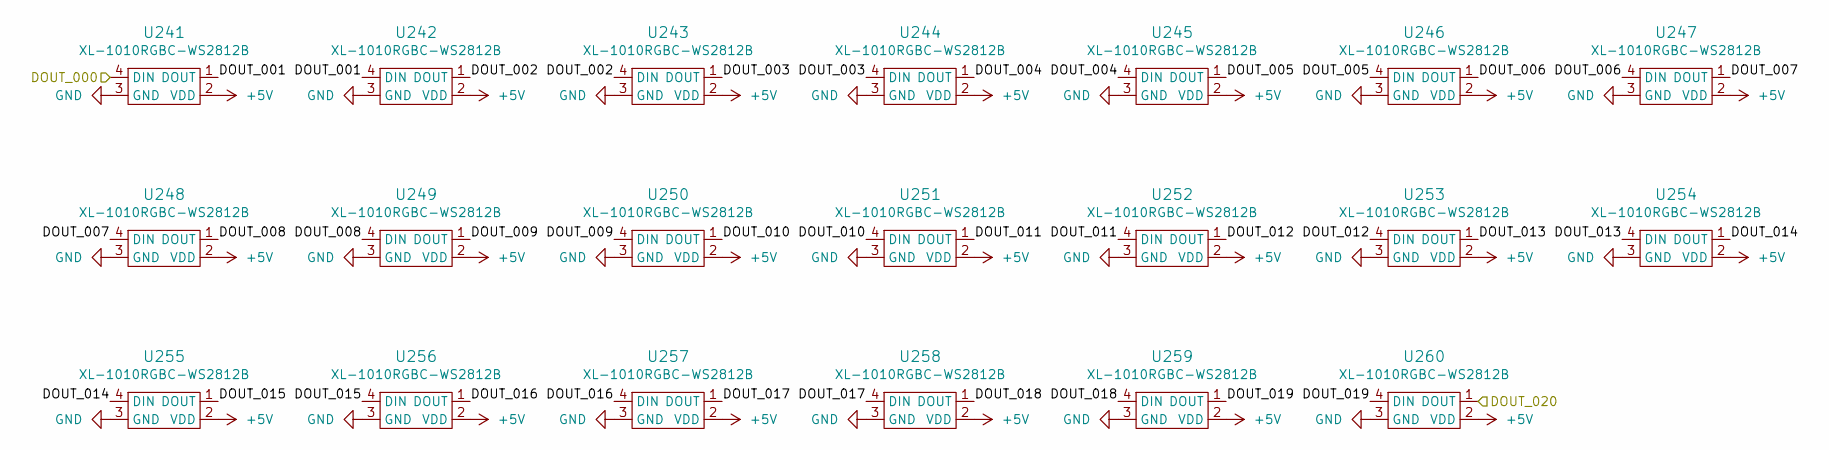
[picture p15: schematic 20xLED_013.kicad_sch]

Parts:
U241, U242, U243, U244, U245, U246, U247, U248, U249, U250, U251, U252, U253, U254, U255, U256, U257, U258, U259, U260: XL-1010RGBC-WS2812B; SMD-4P,1.1x1.1mm; LCSC C5349953

Connections:
+5V: U241.2 (VDD), U242.2 (VDD), U243.2 (VDD), U244.2 (VDD), U245.2 (VDD), U246.2 (VDD), U247.2 (VDD), U248.2 (VDD), U249.2 (VDD), U250.2 (VDD), U251.2 (VDD), U252.2 (VDD), U253.2 (VDD), U254.2 (VDD), U255.2 (VDD), U256.2 (VDD), U257.2 (VDD), U258.2 (VDD), U259.2 (VDD), U260.2 (VDD)
DOUT_000: U241.4 (DIN)
DOUT_001: U241.1 (DOUT), U242.4 (DIN)
DOUT_002: U242.1 (DOUT), U243.4 (DIN)
DOUT_003: U243.1 (DOUT), U244.4 (DIN)
DOUT_004: U244.1 (DOUT), U245.4 (DIN)
DOUT_005: U245.1 (DOUT), U246.4 (DIN)
DOUT_006: U246.1 (DOUT), U247.4 (DIN)
DOUT_007: U247.1 (DOUT), U248.4 (DIN)
DOUT_008: U248.1 (DOUT), U249.4 (DIN)
DOUT_009: U249.1 (DOUT), U250.4 (DIN)
DOUT_010: U250.1 (DOUT), U251.4 (DIN)
DOUT_011: U251.1 (DOUT), U252.4 (DIN)
DOUT_012: U252.1 (DOUT), U253.4 (DIN)
DOUT_013: U253.1 (DOUT), U254.4 (DIN)
DOUT_014: U254.1 (DOUT), U255.4 (DIN)
DOUT_015: U255.1 (DOUT), U256.4 (DIN)
DOUT_016: U256.1 (DOUT), U257.4 (DIN)
DOUT_017: U257.1 (DOUT), U258.4 (DIN)
DOUT_018: U258.1 (DOUT), U259.4 (DIN)
DOUT_019: U259.1 (DOUT), U260.4 (DIN)
DOUT_020: U260.1 (DOUT)
GND: U241.3 (GND), U242.3 (GND), U243.3 (GND), U244.3 (GND), U245.3 (GND), U246.3 (GND), U247.3 (GND), U248.3 (GND), U249.3 (GND), U250.3 (GND), U251.3 (GND), U252.3 (GND), U253.3 (GND), U254.3 (GND), U255.3 (GND), U256.3 (GND), U257.3 (GND), U258.3 (GND), U259.3 (GND), U260.3 (GND)
