elektrojupp/public_transport_map_berlin/hw/20xLED_014.kicad_sch

## KiCad design hw/20xLED_014.kicad_sch (2026-01-20)

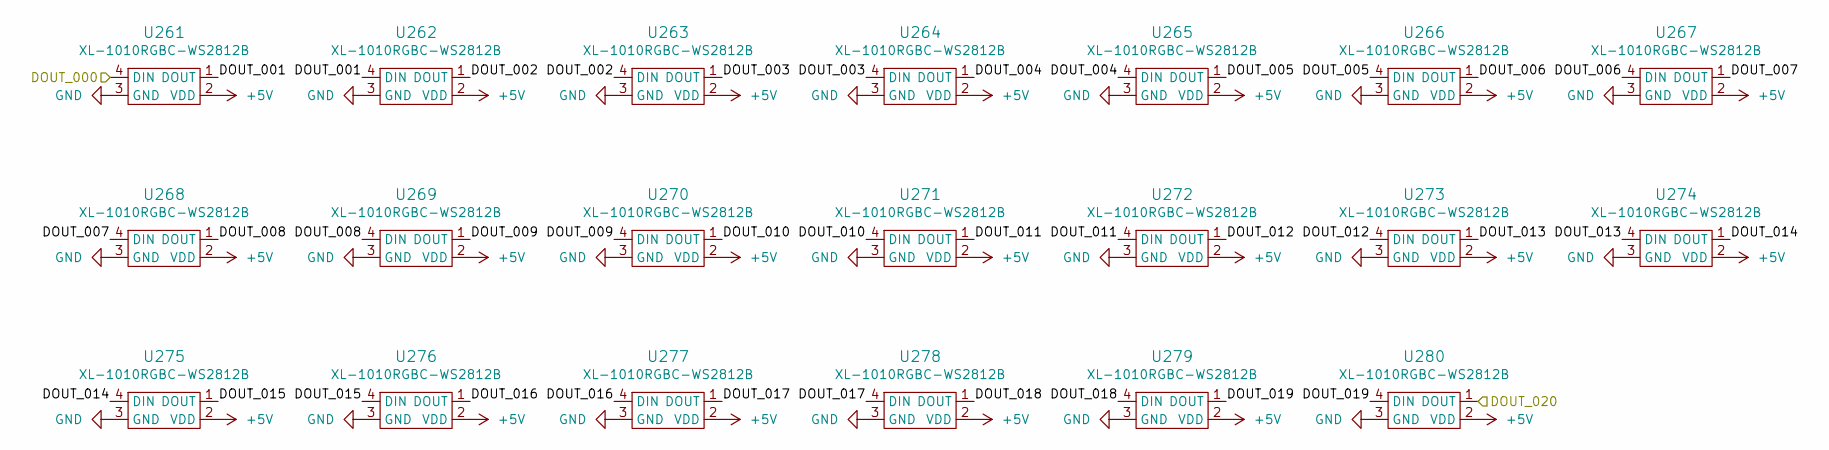
[picture p16: schematic 20xLED_014.kicad_sch]

Parts:
U261, U262, U263, U264, U265, U266, U267, U268, U269, U270, U271, U272, U273, U274, U275, U276, U277, U278, U279, U280: XL-1010RGBC-WS2812B; SMD-4P,1.1x1.1mm; LCSC C5349953

Connections:
+5V: U261.2 (VDD), U262.2 (VDD), U263.2 (VDD), U264.2 (VDD), U265.2 (VDD), U266.2 (VDD), U267.2 (VDD), U268.2 (VDD), U269.2 (VDD), U270.2 (VDD), U271.2 (VDD), U272.2 (VDD), U273.2 (VDD), U274.2 (VDD), U275.2 (VDD), U276.2 (VDD), U277.2 (VDD), U278.2 (VDD), U279.2 (VDD), U280.2 (VDD)
DOUT_000: U261.4 (DIN)
DOUT_001: U261.1 (DOUT), U262.4 (DIN)
DOUT_002: U262.1 (DOUT), U263.4 (DIN)
DOUT_003: U263.1 (DOUT), U264.4 (DIN)
DOUT_004: U264.1 (DOUT), U265.4 (DIN)
DOUT_005: U265.1 (DOUT), U266.4 (DIN)
DOUT_006: U266.1 (DOUT), U267.4 (DIN)
DOUT_007: U267.1 (DOUT), U268.4 (DIN)
DOUT_008: U268.1 (DOUT), U269.4 (DIN)
DOUT_009: U269.1 (DOUT), U270.4 (DIN)
DOUT_010: U270.1 (DOUT), U271.4 (DIN)
DOUT_011: U271.1 (DOUT), U272.4 (DIN)
DOUT_012: U272.1 (DOUT), U273.4 (DIN)
DOUT_013: U273.1 (DOUT), U274.4 (DIN)
DOUT_014: U274.1 (DOUT), U275.4 (DIN)
DOUT_015: U275.1 (DOUT), U276.4 (DIN)
DOUT_016: U276.1 (DOUT), U277.4 (DIN)
DOUT_017: U277.1 (DOUT), U278.4 (DIN)
DOUT_018: U278.1 (DOUT), U279.4 (DIN)
DOUT_019: U279.1 (DOUT), U280.4 (DIN)
DOUT_020: U280.1 (DOUT)
GND: U261.3 (GND), U262.3 (GND), U263.3 (GND), U264.3 (GND), U265.3 (GND), U266.3 (GND), U267.3 (GND), U268.3 (GND), U269.3 (GND), U270.3 (GND), U271.3 (GND), U272.3 (GND), U273.3 (GND), U274.3 (GND), U275.3 (GND), U276.3 (GND), U277.3 (GND), U278.3 (GND), U279.3 (GND), U280.3 (GND)
