elektrojupp/public_transport_map_berlin/hw/20xLED_015.kicad_sch

## KiCad design hw/20xLED_015.kicad_sch (2026-01-20)

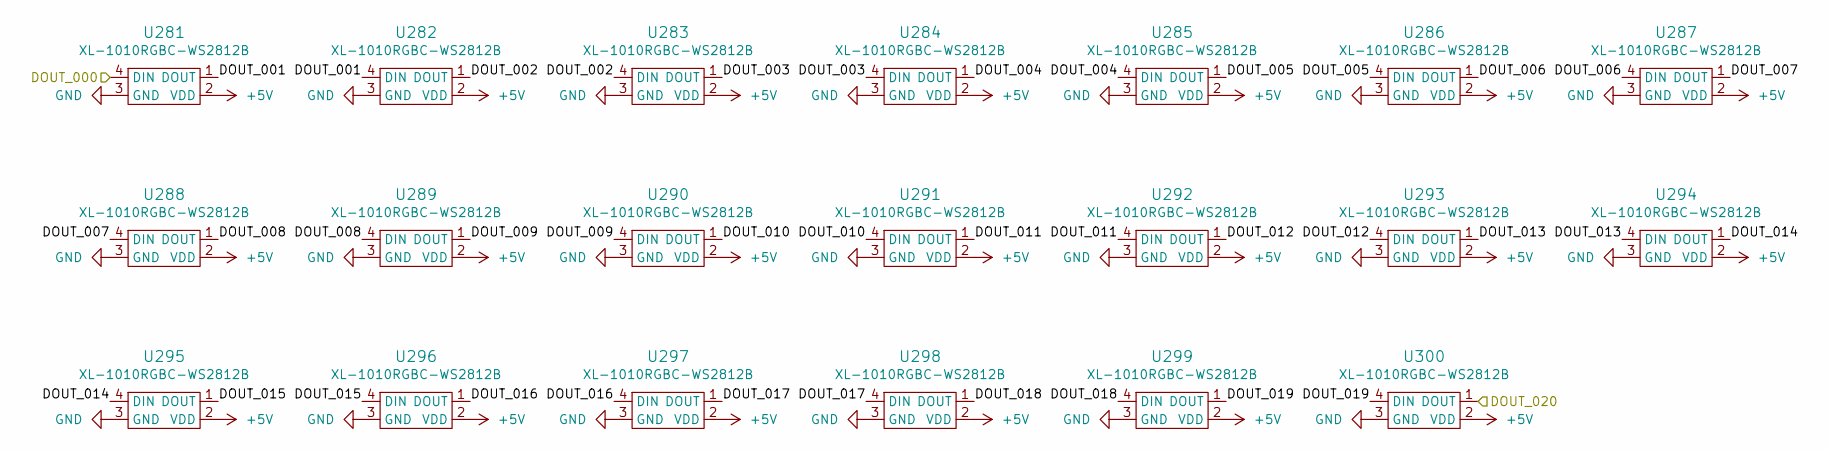
[picture p17: schematic 20xLED_015.kicad_sch]

Parts:
U281, U282, U283, U284, U285, U286, U287, U288, U289, U290, U291, U292, U293, U294, U295, U296, U297, U298, U299, U300: XL-1010RGBC-WS2812B; SMD-4P,1.1x1.1mm; LCSC C5349953

Connections:
+5V: U281.2 (VDD), U282.2 (VDD), U283.2 (VDD), U284.2 (VDD), U285.2 (VDD), U286.2 (VDD), U287.2 (VDD), U288.2 (VDD), U289.2 (VDD), U290.2 (VDD), U291.2 (VDD), U292.2 (VDD), U293.2 (VDD), U294.2 (VDD), U295.2 (VDD), U296.2 (VDD), U297.2 (VDD), U298.2 (VDD), U299.2 (VDD), U300.2 (VDD)
DOUT_000: U281.4 (DIN)
DOUT_001: U281.1 (DOUT), U282.4 (DIN)
DOUT_002: U282.1 (DOUT), U283.4 (DIN)
DOUT_003: U283.1 (DOUT), U284.4 (DIN)
DOUT_004: U284.1 (DOUT), U285.4 (DIN)
DOUT_005: U285.1 (DOUT), U286.4 (DIN)
DOUT_006: U286.1 (DOUT), U287.4 (DIN)
DOUT_007: U287.1 (DOUT), U288.4 (DIN)
DOUT_008: U288.1 (DOUT), U289.4 (DIN)
DOUT_009: U289.1 (DOUT), U290.4 (DIN)
DOUT_010: U290.1 (DOUT), U291.4 (DIN)
DOUT_011: U291.1 (DOUT), U292.4 (DIN)
DOUT_012: U292.1 (DOUT), U293.4 (DIN)
DOUT_013: U293.1 (DOUT), U294.4 (DIN)
DOUT_014: U294.1 (DOUT), U295.4 (DIN)
DOUT_015: U295.1 (DOUT), U296.4 (DIN)
DOUT_016: U296.1 (DOUT), U297.4 (DIN)
DOUT_017: U297.1 (DOUT), U298.4 (DIN)
DOUT_018: U298.1 (DOUT), U299.4 (DIN)
DOUT_019: U299.1 (DOUT), U300.4 (DIN)
DOUT_020: U300.1 (DOUT)
GND: U281.3 (GND), U282.3 (GND), U283.3 (GND), U284.3 (GND), U285.3 (GND), U286.3 (GND), U287.3 (GND), U288.3 (GND), U289.3 (GND), U290.3 (GND), U291.3 (GND), U292.3 (GND), U293.3 (GND), U294.3 (GND), U295.3 (GND), U296.3 (GND), U297.3 (GND), U298.3 (GND), U299.3 (GND), U300.3 (GND)
