elektrojupp/public_transport_map_berlin/hw/20xLED_016.kicad_sch

## KiCad design hw/20xLED_016.kicad_sch (2026-01-20)

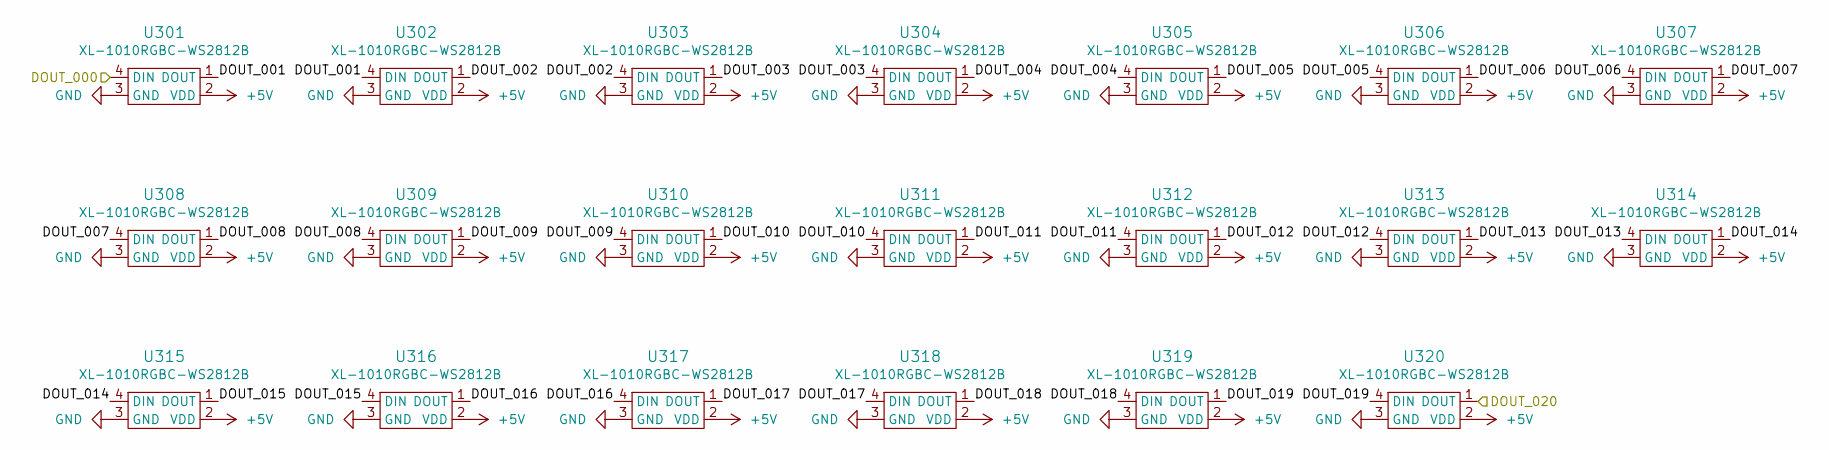
[picture p18: schematic 20xLED_016.kicad_sch]

Parts:
U301, U302, U303, U304, U305, U306, U307, U308, U309, U310, U311, U312, U313, U314, U315, U316, U317, U318, U319, U320: XL-1010RGBC-WS2812B; SMD-4P,1.1x1.1mm; LCSC C5349953

Connections:
+5V: U301.2 (VDD), U302.2 (VDD), U303.2 (VDD), U304.2 (VDD), U305.2 (VDD), U306.2 (VDD), U307.2 (VDD), U308.2 (VDD), U309.2 (VDD), U310.2 (VDD), U311.2 (VDD), U312.2 (VDD), U313.2 (VDD), U314.2 (VDD), U315.2 (VDD), U316.2 (VDD), U317.2 (VDD), U318.2 (VDD), U319.2 (VDD), U320.2 (VDD)
DOUT_000: U301.4 (DIN)
DOUT_001: U301.1 (DOUT), U302.4 (DIN)
DOUT_002: U302.1 (DOUT), U303.4 (DIN)
DOUT_003: U303.1 (DOUT), U304.4 (DIN)
DOUT_004: U304.1 (DOUT), U305.4 (DIN)
DOUT_005: U305.1 (DOUT), U306.4 (DIN)
DOUT_006: U306.1 (DOUT), U307.4 (DIN)
DOUT_007: U307.1 (DOUT), U308.4 (DIN)
DOUT_008: U308.1 (DOUT), U309.4 (DIN)
DOUT_009: U309.1 (DOUT), U310.4 (DIN)
DOUT_010: U310.1 (DOUT), U311.4 (DIN)
DOUT_011: U311.1 (DOUT), U312.4 (DIN)
DOUT_012: U312.1 (DOUT), U313.4 (DIN)
DOUT_013: U313.1 (DOUT), U314.4 (DIN)
DOUT_014: U314.1 (DOUT), U315.4 (DIN)
DOUT_015: U315.1 (DOUT), U316.4 (DIN)
DOUT_016: U316.1 (DOUT), U317.4 (DIN)
DOUT_017: U317.1 (DOUT), U318.4 (DIN)
DOUT_018: U318.1 (DOUT), U319.4 (DIN)
DOUT_019: U319.1 (DOUT), U320.4 (DIN)
DOUT_020: U320.1 (DOUT)
GND: U301.3 (GND), U302.3 (GND), U303.3 (GND), U304.3 (GND), U305.3 (GND), U306.3 (GND), U307.3 (GND), U308.3 (GND), U309.3 (GND), U310.3 (GND), U311.3 (GND), U312.3 (GND), U313.3 (GND), U314.3 (GND), U315.3 (GND), U316.3 (GND), U317.3 (GND), U318.3 (GND), U319.3 (GND), U320.3 (GND)
