elektrojupp/public_transport_map_berlin/hw/berlin_bahn.kicad_sch

## KiCad design hw/berlin_bahn.kicad_sch (2026-01-20)

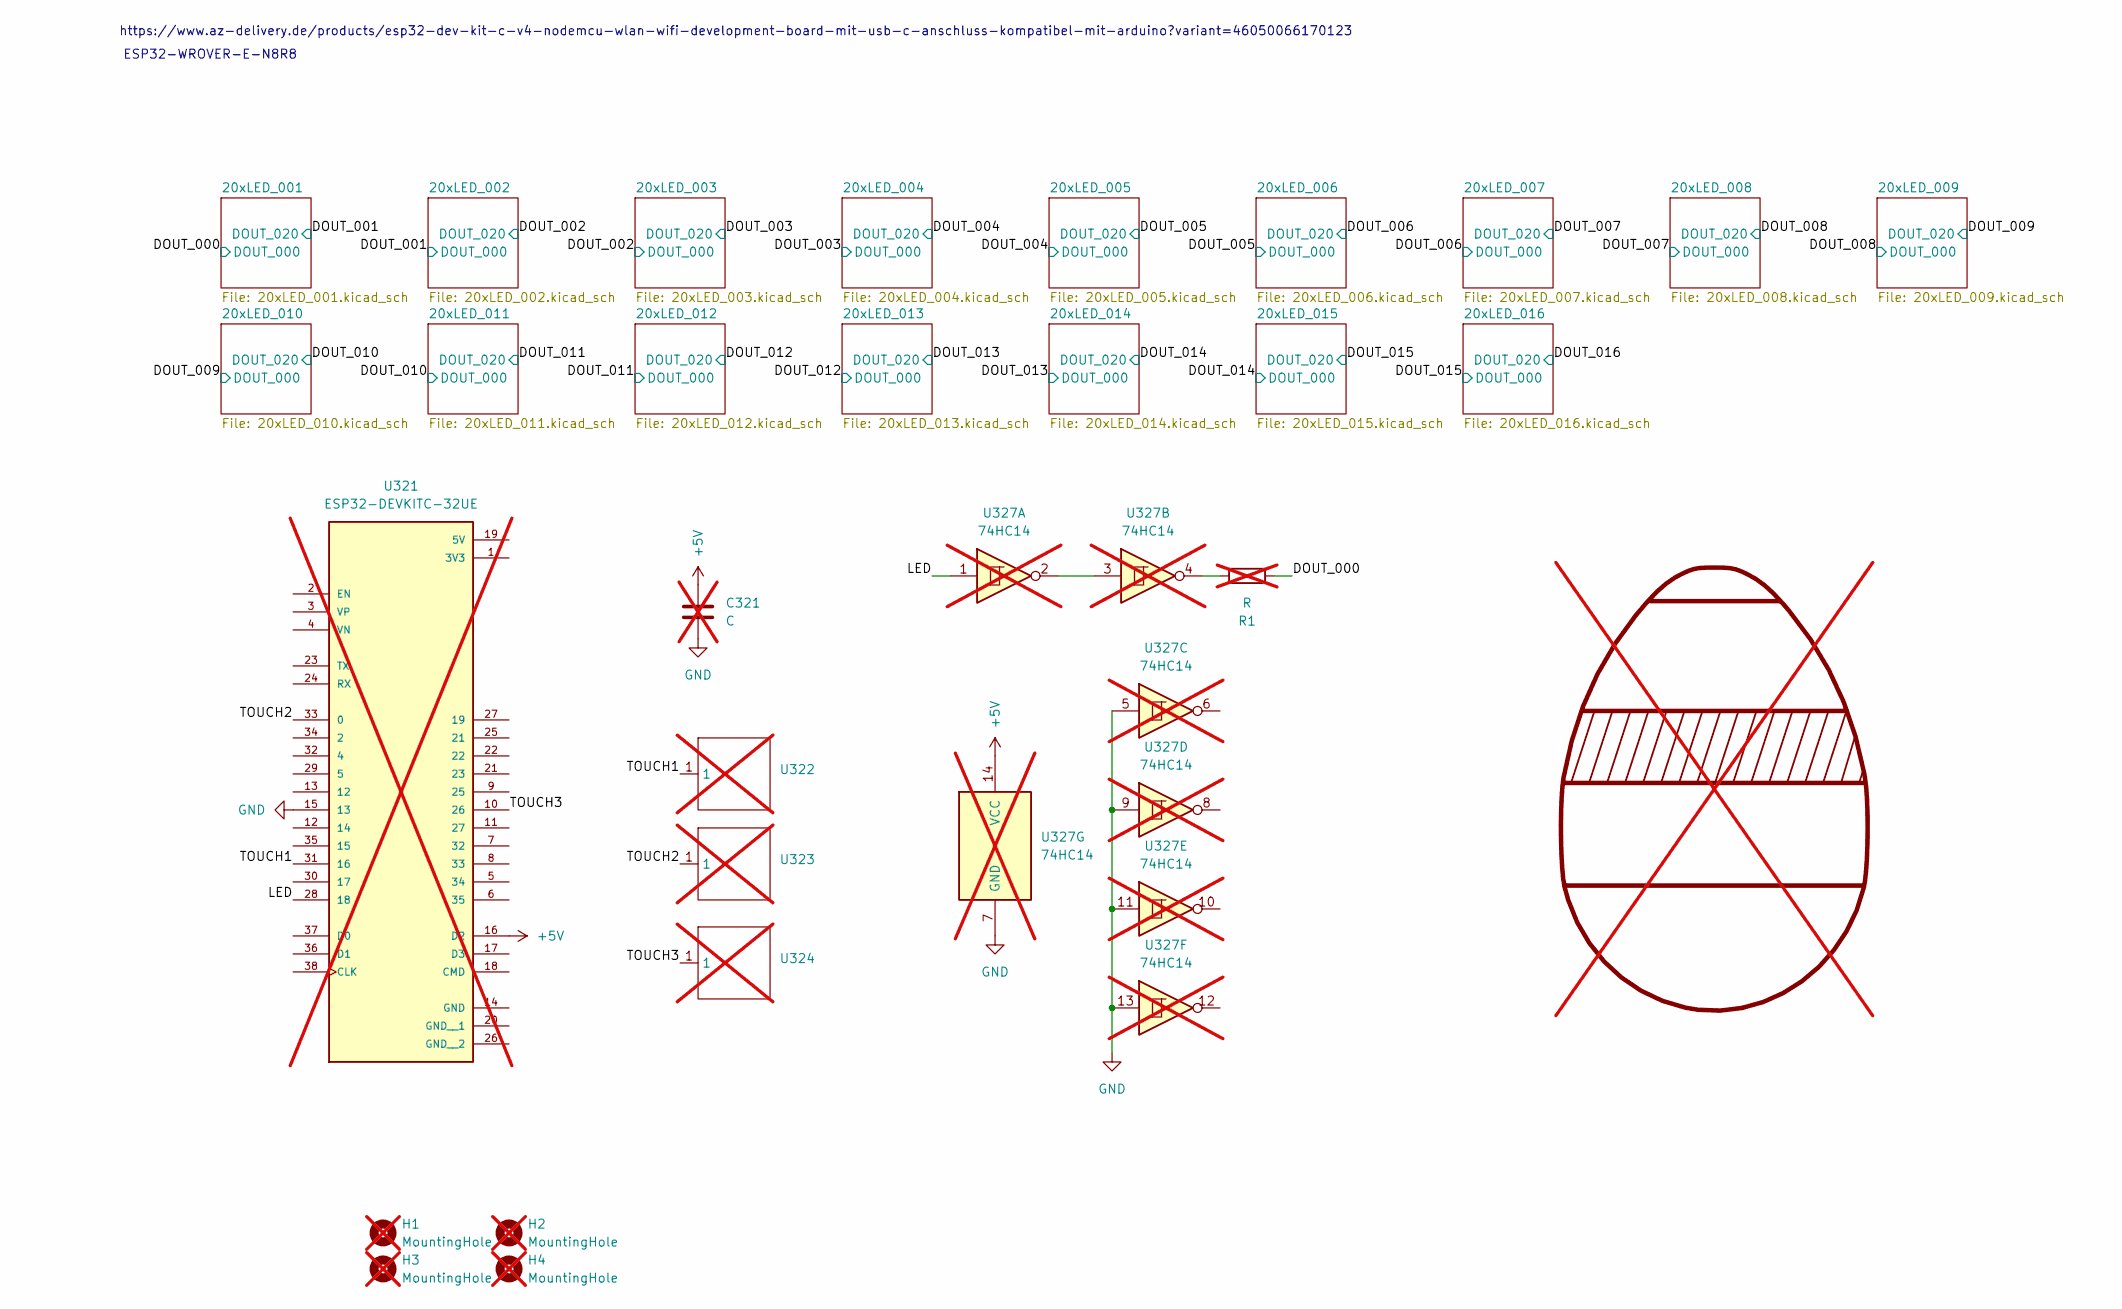
[picture p19: schematic berlin_bahn.kicad_sch]

Parts:
C321: C; CP_Elec_8x10; not fitted
H1, H2, H3, H4: MountingHole; MountingHole_2.2mm_M2_DIN965_Pad; not fitted
R1: R; R_0805_2012Metric_Pad1.20x1.40mm_HandSolder; not fitted
SYM1: SYM_EasterEgg_42x60mm; Logo_Elektrojupp; not fitted
U321: ESP32-DEVKITC-32UE; ESPRESSIF_ESP32-DEVKITC-32UE; PARTREV V4; not fitted
U322, U323, U324: cap_touch; not fitted
U327: 74HC14; SOIC-14_3.9x8.7mm_P1.27mm; not fitted

Connections:
+5V: C321.1, U321.16 (D2), U327.14 (VCC)
DOUT_000: R1.1
GND: C321.2, U321.15 (13), U327.5, U327.7 (GND), U327.9, U327.11, U327.13
LED: U321.28 (18), U327.1
unnamed: R1.2, U327.4
unnamed: U327.2, U327.3
TOUCH1: U321.31 (16), U322.1
TOUCH2: U321.33 (0), U323.1
TOUCH3: U321.10 (26), U324.1

Notes on the sheet:
https://www.az-delivery.de/products/esp32-dev-kit-c-v4-nodemcu-wlan-wifi-development-board-mit-usb-c-anschluss-kompatibel-mit-arduino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
ESP32-WROVER-E-N8R8
