elektrojupp/public_transport_map_berlin/hw/esp_con.kicad_sch

## KiCad design hw/esp_con.kicad_sch (2026-01-20)

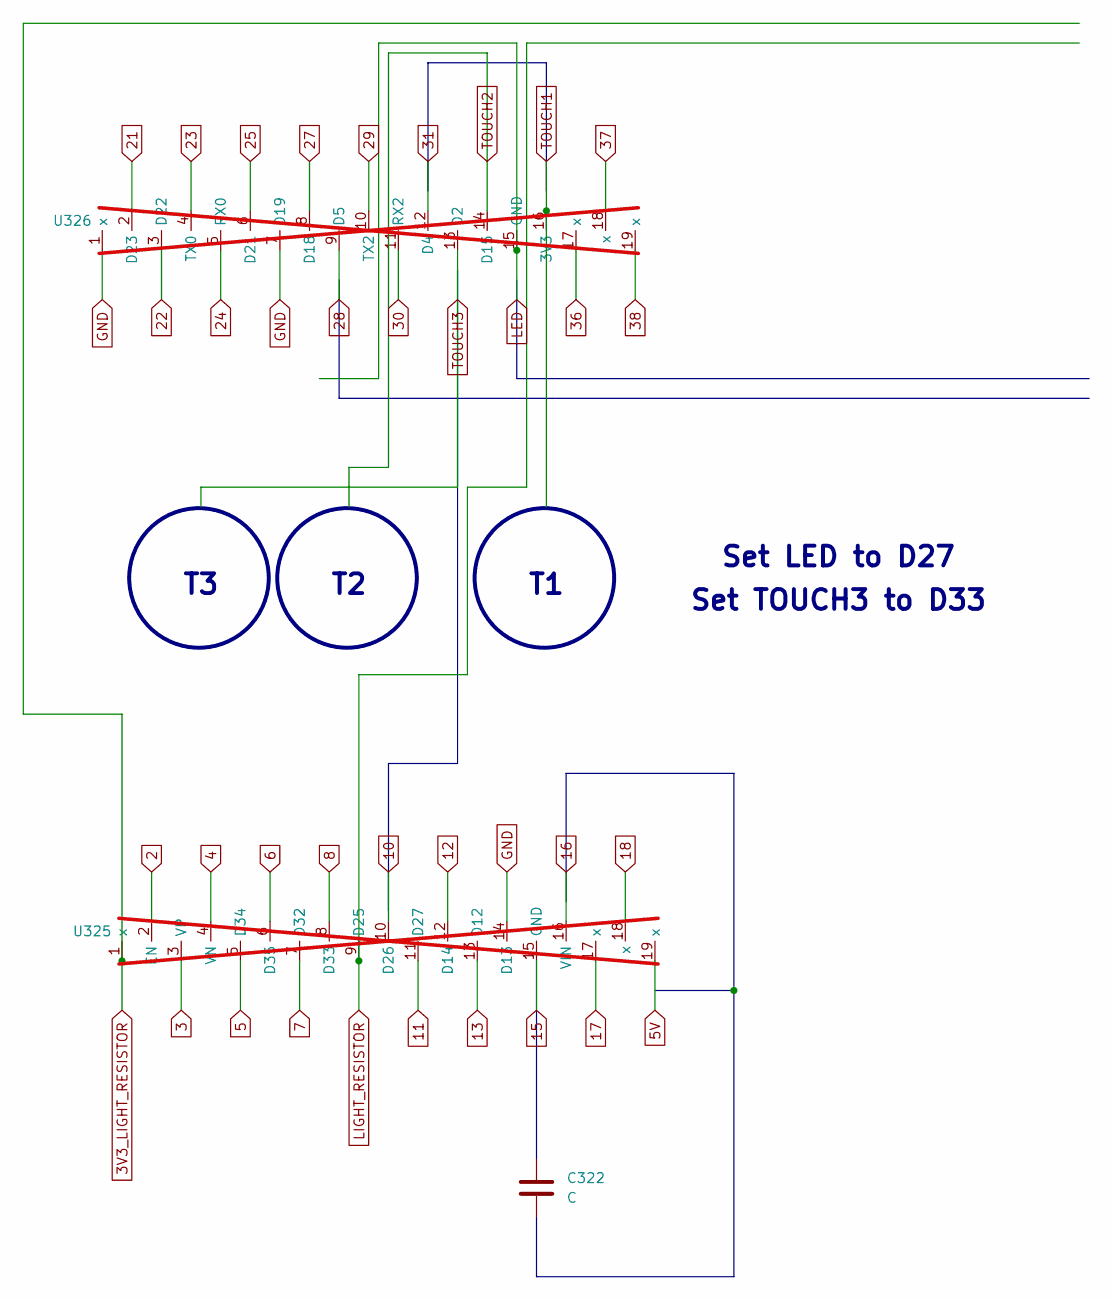
[picture p20: schematic esp_con.kicad_sch]

Parts:
C322: C
U325, U326: not fitted

Connections:
2: U325.2 (EN)
3: U325.3 (VP)
3V3_LIGHT_RESISTOR: U325.1 (x)
4: U325.4 (VN)
5: U325.5 (D34)
5V: U325.19 (x)
6: U325.6 (D35)
7: U325.7 (D32)
8: U325.8 (D33)
10: U325.10 (D26)
11: U325.11 (D27)
12: U325.12 (D14)
13: U325.13 (D12)
15: U325.15 (GND)
16: U325.16 (VIN)
17: U325.17 (x)
18: U325.18 (x)
21: U326.2 (D23)
22: U326.3 (D22)
23: U326.4 (TX0)
24: U326.5 (RX0)
25: U326.6 (D21)
27: U326.8 (D18)
28: U326.9 (D5)
29: U326.10 (TX2)
30: U326.11 (RX2)
31: U326.12 (D4)
36: U326.17 (x)
37: U326.18 (x)
38: U326.19 (x)
GND: U325.14 (D13), U326.1 (x), U326.7 (D19)
LED: U326.15 (GND)
LIGHT_RESISTOR: U325.9 (D25)
TOUCH1: U326.16 (3V3)
TOUCH2: U326.14 (D15)
TOUCH3: U326.13 (D2)

Notes on the sheet:
Set LED to D27
Set TOUCH3 to D33
