elektrojupp/public_transport_map_berlin/sw/src/user/src/line_data.c

#include "line_data.h"


uint8_t led_active[320] = {0};
 

// 900057102
// led nmer on pcb -1
station_line_t stations[] = {
    {900170004, 8},
    {900170003, 9},
    {900170002, 10},
    {900170001, 11},
    {900170005, 12},
    {900175010, 13},
    {900175015, 14},
    {900175007, 15},
    {900175006, 16},
    {900175005, 17},
    {900175004, 18},
    {900175001, 19},
    {900171001, 20},
    {900171003, 21},
    {900152002, 22},
    {900152001, 23},
    {900151001, 24},
    {900110002, 25},
    {900110003, 26},
    {900110004, 27},
    {900110012, 28},
    {900120009, 29},
    {900120008, 30},
    {900120025, 31},
    {900120006, 32},
    {900100017, 33},
    {900100003, 34},
    {900100045, 35},
    {900100014, 36},
    {900100013, 37},
    {900100537, 38},
    {900100513, 39},
    {900100002, 40},
    {900007103, 41},
    {900007110, 42},
    {900100023, 43},
    {900100051, 44},
    {900100016, 45},
    {900110005, 46},
    {900110006, 47},
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
    {900024106, 187}, // duplicate line_pos 187 in your list
    {900024101, 190}, // duplicate line_pos 187 in your list
    {900057102, 132}
};




typedef enum
{
LINE_U1 = 0,
LINE_U2 = 1,
LINE_U3 = 2,
LINE_U4 = 3,
LINE_U5 = 4,
LINE_U6 = 5,
LINE_U7 = 6,
LINE_U8 = 7,
LINE_U9 = 8,
LINE_S1 = 9,
LINE_S2 = 10,
LINE_S25 = 11,
LINE_S26 = 12,
LINE_S3 = 13,
LINE_S5 = 14,
LINE_S7 = 15,
LINE_S75 = 16,
LINE_S8 = 17,
LINE_S85 = 18,
LINE_S9 = 19,
LINE_S41 = 20,
LINE_S42 = 21,
LINE_S45 = 22,
LINE_S46 = 23,
LINE_S47 = 24,
LINE_S41S42 = 25
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
}

// 9:
// 1,2,3,4,6,7
static void draw_9(led_strip_handle_t *led_strip, uint8_t r, uint8_t g, uint8_t b)
{
  seg_1(led_strip, r, g, b);
  seg_2(led_strip, r, g, b);
  seg_3(led_strip, r, g, b);
  //seg_4(led_strip, r, g, b);
  seg_6(led_strip, r, g, b);
  seg_7(led_strip, r, g, b);
}

// 0:
// 1,2,3,4,5,6
static void draw_0(led_strip_handle_t *led_strip, uint8_t r, uint8_t g, uint8_t b)
{
  seg_1(led_strip, r, g, b);
  seg_2(led_strip, r, g, b);
  seg_3(led_strip, r, g, b);
  seg_4(led_strip, r, g, b);
  seg_5(led_strip, r, g, b);
  seg_6(led_strip, r, g, b);
}

// S:
// 1,3,7
static void draw_S(led_strip_handle_t *led_strip, uint8_t r, uint8_t g, uint8_t b)
{
  seg_1(led_strip, r, g, b);
  seg_6(led_strip, r, g, b);
  seg_3(led_strip, r, g, b);
  seg_7(led_strip, r, g, b);
  seg_4(led_strip, r, g, b);
}

// U:
// 1,2,3,5,6
static void draw_U(led_strip_handle_t *led_strip, uint8_t r, uint8_t g, uint8_t b)
{
  //seg_1(led_strip, r, g, b);
  //seg_2(led_strip, r, g, b);
  seg_7(led_strip, r, g, b);
  seg_2(led_strip, r, g, b);
  seg_6(led_strip, r, g, b);
}

void line_data_draw_string(char * str, uint32_t len, led_strip_handle_t *led_strip, uint8_t r, uint8_t g, uint8_t b, uint32_t on_time, uint32_t off_time)
{
  for(int i = 0; i < len; i ++)
  {
    
    for(int j = 0; j < 320; j ++)
    {
      ESP_ERROR_CHECK(led_strip_set_pixel(*led_strip, j, 0, 0, 0));
    }

    char chr = str[i];
    switch(chr) {
      case 0: 
        vTaskDelay(pdMS_TO_TICKS(on_time+off_time)); 
        break;
      case '0': 
        draw_0(led_strip, r, g, b); 
        break;
      case '1':
        draw_1(led_strip, r, g, b); 
        break;
      case '2':
        draw_2(led_strip, r, g, b); 
        break;      
      case '3':
        draw_3(led_strip, r, g, b); 
        break;      
      case '4':
        draw_4(led_strip, r, g, b); 
        break;      
      case '5':
        draw_5(led_strip, r, g, b); 
        break;      
      case '6':
        draw_6(led_strip, r, g, b); 
        break;      
      case '7':
        draw_7(led_strip, r, g, b); 
        break;      
      case '8':
        draw_8(led_strip, r, g, b); 
        break;      
      case '9':
        draw_9(led_strip, r, g, b); 
        break;      
      case 'S':
        draw_S(led_strip, r, g, b); 
        break;      
      case 'U':
        draw_U(led_strip, r, g, b); 
        break;      
      default: break;
    }
    ESP_ERROR_CHECK(led_strip_refresh(*led_strip));
    vTaskDelay(pdMS_TO_TICKS(on_time)); 
    if(off_time != 0)
    {
      for(int j = 0; j < 320; j ++)
      {
        ESP_ERROR_CHECK(led_strip_set_pixel(*led_strip, j, 0, 0, 0));
      }
      ESP_ERROR_CHECK(led_strip_refresh(*led_strip));
      vTaskDelay(pdMS_TO_TICKS(off_time)); 
    }
  }
}


void led_state_draw_all_lines(led_strip_handle_t *led_strip, uint32_t on_time, uint32_t off_time)
{
  for(int i = 0; i < line_data_number_of_lines(); i ++)
  {
    line_data_draw_string(leds[i].name, strlen(leds[i].name), led_strip, leds[i].r/10, leds[i].g/10, leds[i].b/10, on_time, off_time);
  }
}

void led_state_draw_line(led_strip_handle_t *led_strip, uint32_t line_nr, uint32_t on_time, uint32_t off_time)
{
  line_data_draw_string(leds[line_nr].name, strlen(leds[line_nr].name), led_strip, leds[line_nr].r/10, leds[line_nr].g/10, leds[line_nr].b/10, on_time, off_time);
  for(int j = 0; j < 320; j ++)
  {
    ESP_ERROR_CHECK(led_strip_set_pixel(*led_strip, j, 0, 0, 0));
  }
  print_line(led_strip, line_nr);
  ESP_ERROR_CHECK(led_strip_refresh(*led_strip));
  vTaskDelay(pdMS_TO_TICKS(1000)); 
}


void draw_all_numbers(led_strip_handle_t *led_strip)
{
  int time_on = 1000;
  int time_off = 100;
  line_data_draw_string("0", 1, led_strip, 0, 0, 1, time_on, time_off);
  line_data_draw_string("1", 1, led_strip, 0, 0, 1, time_on, time_off);
  line_data_draw_string("2", 1, led_strip, 0, 0, 1, time_on, time_off);
  line_data_draw_string("3", 1, led_strip, 0, 0, 1, time_on, time_off);
  line_data_draw_string("4", 1, led_strip, 0, 0, 1, time_on, time_off);
  line_data_draw_string("5", 1, led_strip, 0, 0, 1, time_on, time_off);
  line_data_draw_string("6", 1, led_strip, 0, 0, 1, time_on, time_off);
  line_data_draw_string("7", 1, led_strip, 0, 0, 1, time_on, time_off);
  line_data_draw_string("8", 1, led_strip, 0, 0, 1, time_on, time_off);
  line_data_draw_string("9", 1, led_strip, 0, 0, 1, time_on, time_off);
  line_data_draw_string("U", 1, led_strip, 0, 0, 1, time_on, time_off);
  line_data_draw_string("S", 1, led_strip, 0, 0, 1, time_on, time_off);

}

void print_line(led_strip_handle_t *led_strip, int8_t line_nr) {
    line_data_struct_t *led = &leds[line_nr];
    for(uint32_t y = 0; y < led->pos_size; y ++)
    {
        ESP_ERROR_CHECK(led_strip_set_pixel(*led_strip, led->pos[y].pos_station, led->g/10, led->r/10, led->b/10));
    }
}


/*




1:
2,3

2:
1,2,7,5,4

3:
1,2,7,3,4

4:
6,7,2,3

5:
1,6,7,3,4

6:
1,6,7,3,4,5

7:
1,2,3

8:
1,2,3,4,5,6,7

9:
1,2,3,4,6,7

0:
1,2,3,4,5,6

S:
1,7,3

U:
1,2,3,5,6


 1 1 1 1 
6       2
6       2
6       2
6       2
 7 7 7 7       
5       3
5       3
5       3
5       3
 4 4 4 4
                            
                             
                             
1
stadtmitte 240
hausvogtei 241
spittelmarkt 38
märkisches 37
heinrich heine 245

2
heinrich heine 245
moritzplatz 251
kotti 254
schönlein 252
herrmannplatz 253

3
herrmannplatz 253
boddinstr 255
leinestr 256
hermannstr 257


4.
hermannstr 257
tempelhof 232


5
tempelhof 232
paradestraße 233
platz ad luft 234
mehringdamm 235


6
mehringdamm 235
prinzenstr 237
charlie 239
stadtmitte 240

7
mehringdamm 235
gneisenaustraße 236
südstern 243
kotti 254





                             
1
240
241
38
37
245

2
245
251
254
252
253

3
253
255
256
257


4.
257
232


5
232
233
234
235


6
235
237
239
240

7
235
236
243
254





*/
