elektrojupp/public_transport_map_berlin/sw/src/user/inc/led.h

#ifndef __LED_STRIPE_H_
#define __LED_STRIPE_H_

void led_stripe_run(void);
void led_stripe_init(void);
void display_chance_to_reset_provisioning_pattern(void);
void fiddle_as_lon_as_init(void);

#endif //__LED_STRIPE_H_
